jace-xu/Control-esp32/Structure/机械臂_v6/板材/旋转台底板_5mm.SLDPRT

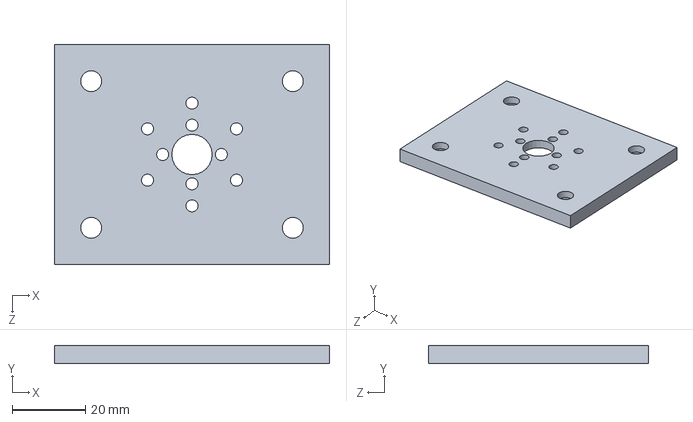
[picture p15: CAD file, 2026-09-05]
Structure/机械臂_v6/板材/旋转台底板_5mm.SLDPRT
75.0 x 5.00 x 60.0 mm
