jace-xu/Control-esp32/Structure/机械臂_v6/购买标准件/丝杆_8_250.SLDPRT

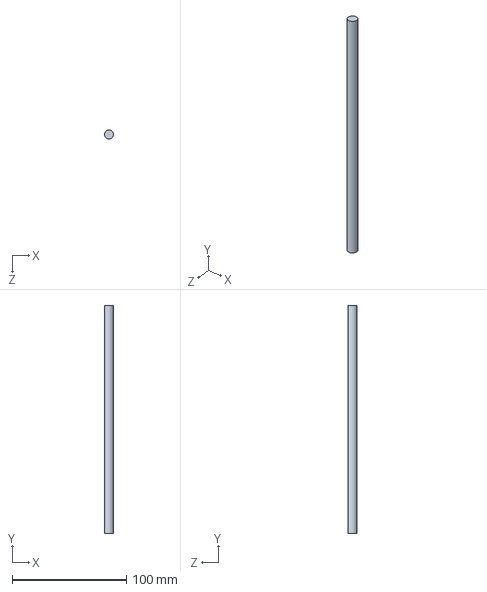
[picture p16: CAD file, 2026-09-05]
Structure/机械臂_v6/购买标准件/丝杆_8_250.SLDPRT
8.00 x 200.0 x 8.00 mm
