jace-xu/Control-esp32/Structure/物料.SLDPRT

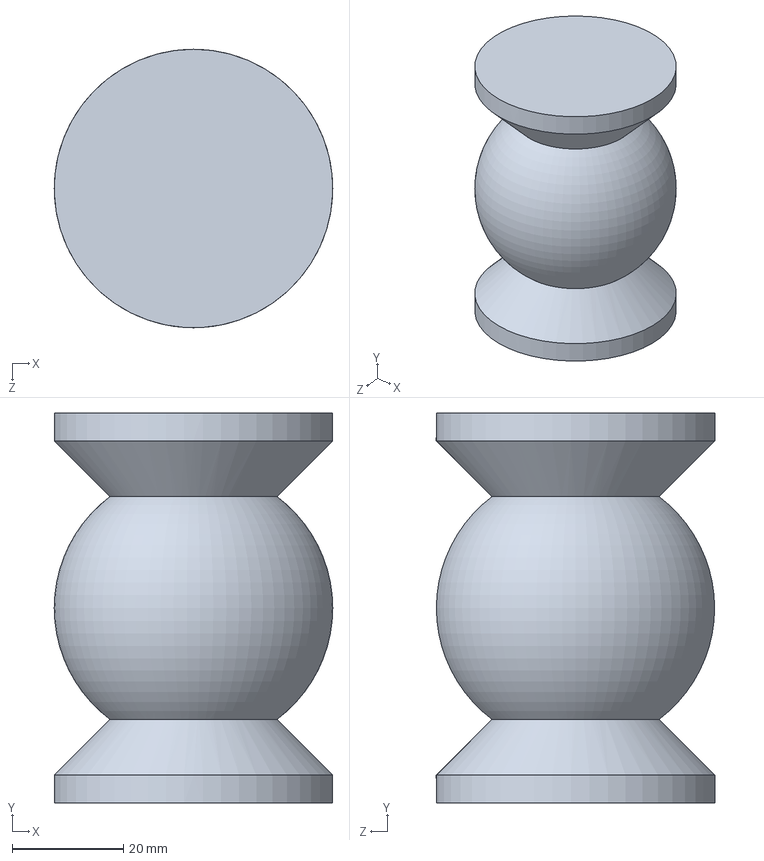
[picture p17: CAD file, 2026-09-05]
Structure/物料.SLDPRT
50.0 x 70.0 x 50.0 mm
