jace-xu/Control-esp32/Structure/物流小车底盘_v6/底盘/板材/电机连接板_后.SLDPRT

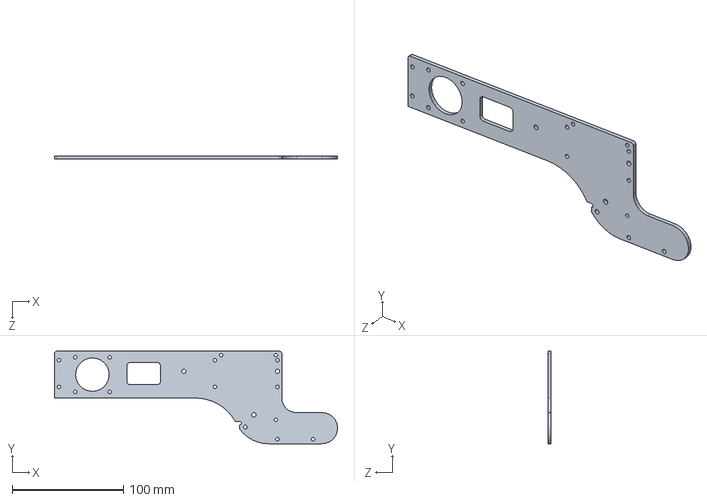
[picture p19: CAD file, 2026-09-05]
Structure/物流小车底盘_v6/底盘/板材/电机连接板_后.SLDPRT
253.9 x 83.0 x 3.00 mm
