jace-xu/Control-esp32/Structure/物流小车底盘_v6/底盘/购买件/麦轮联轴器.SLDPRT

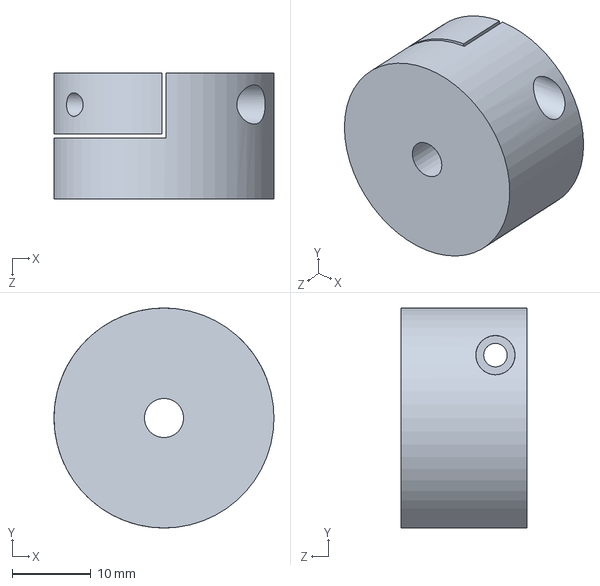
[picture p20: CAD file, 2026-09-05]
Structure/物流小车底盘_v6/底盘/购买件/麦轮联轴器.SLDPRT
28.0 x 28.0 x 16.0 mm
