jace-xu/Control-esp32/Structure/物流小车底盘_v6/标准件/mg996r.SLDPRT

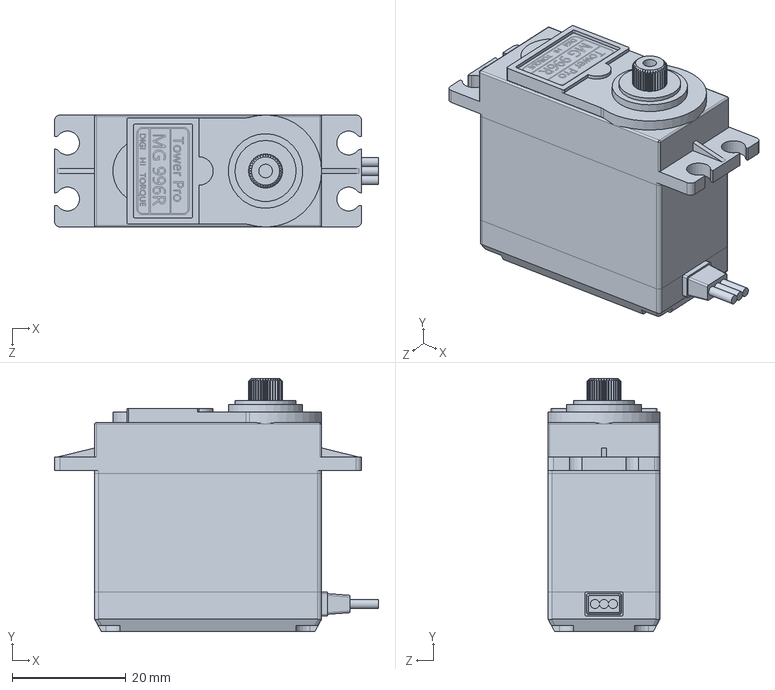
[picture p21: CAD file, 2026-09-05]
Structure/物流小车底盘_v6/标准件/mg996r.SLDPRT
57.0 x 44.5 x 19.7 mm
