jace-xu/Control-esp32/Structure/物流小车底盘_v6/铜柱_m2.5_10.SLDPRT

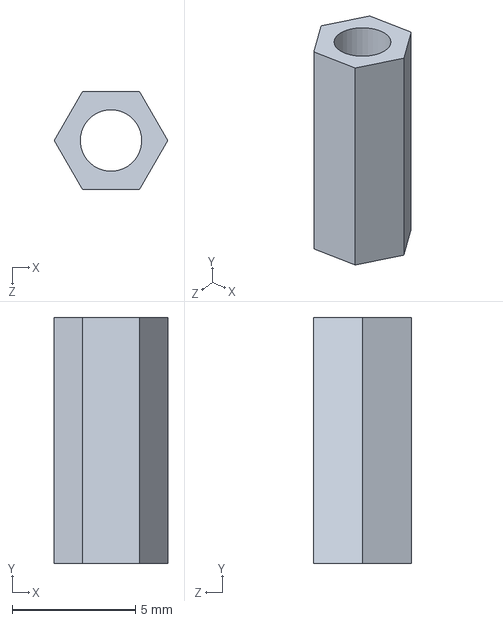
[picture p22: CAD file, 2026-09-05]
Structure/物流小车底盘_v6/铜柱_m2.5_10.SLDPRT
4.62 x 10.0 x 4.00 mm
