jace-xu/Control-esp32/Structure/机械臂_v6/打印件/轴承垫块.SLDPRT

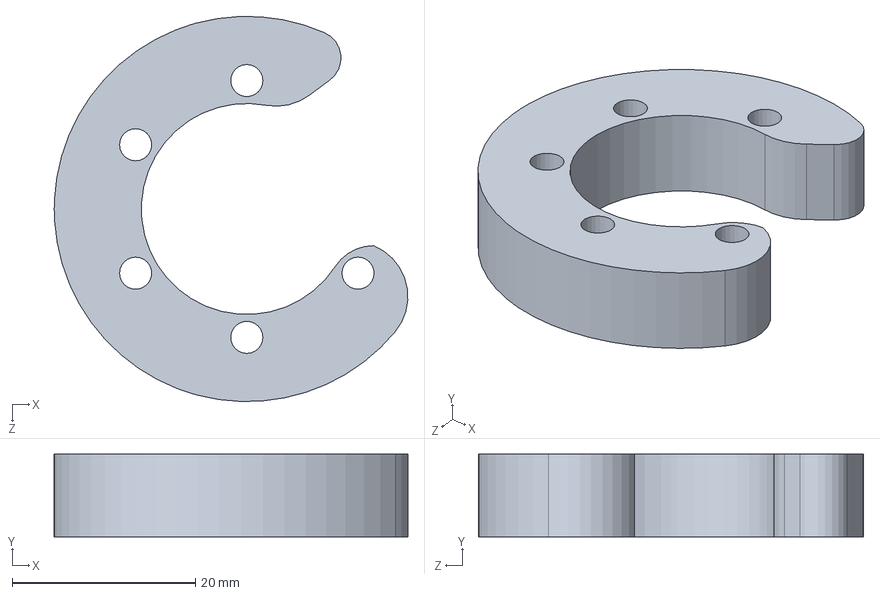
[picture p23: CAD file, 2026-09-05]
Structure/机械臂_v6/打印件/轴承垫块.SLDPRT
38.5 x 9.00 x 42.0 mm
