jace-xu/Control-esp32/Structure/机械臂_v6/板材/夹爪连接板_3mm.SLDPRT

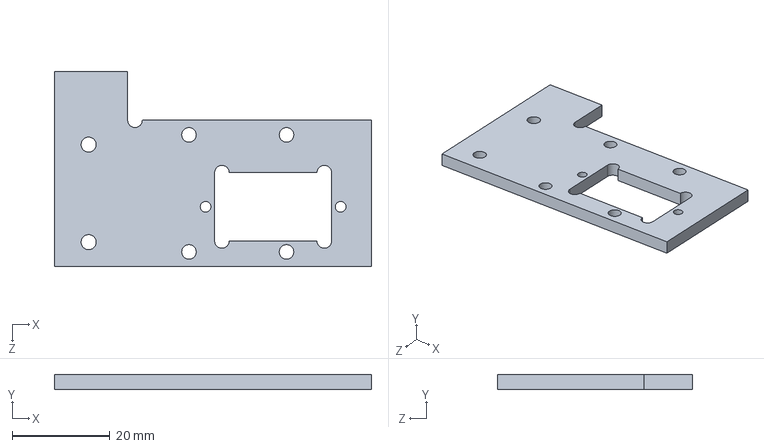
[picture p24: CAD file, 2026-09-05]
Structure/机械臂_v6/板材/夹爪连接板_3mm.SLDPRT
65.0 x 3.00 x 40.0 mm
