jace-xu/Control-esp32/Structure/机械臂_v6/购买标准件/滑块MGN7C_标件_01.SLDPRT

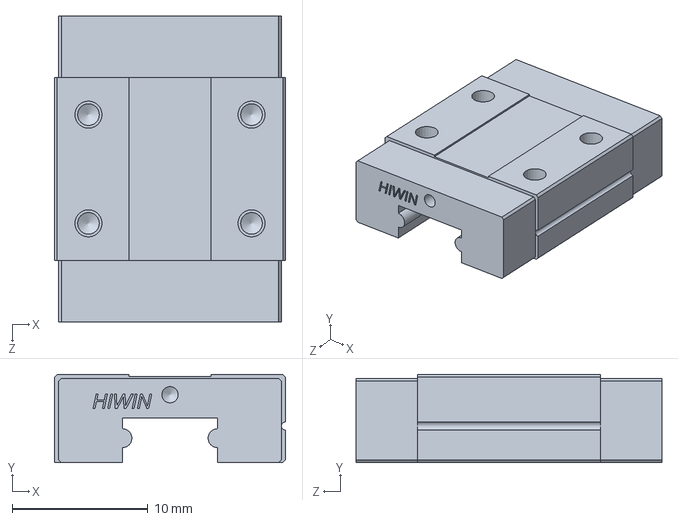
[picture p25: CAD file, 2026-09-05]
Structure/机械臂_v6/购买标准件/滑块MGN7C_标件_01.SLDPRT
17.0 x 6.50 x 22.5 mm
