jace-xu/Control-esp32/Structure/物流小车底盘_v6/底盘/打印件/电机板固定件.SLDPRT

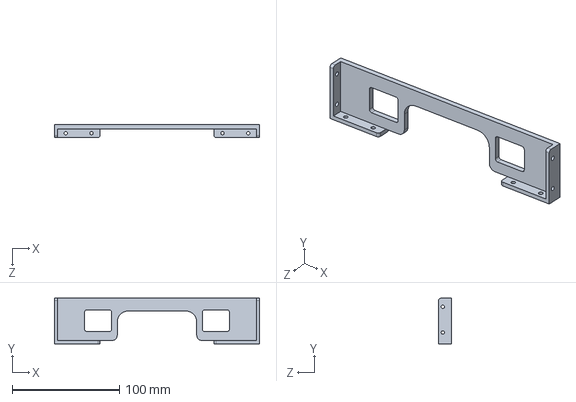
[picture p26: CAD file, 2026-09-05]
Structure/物流小车底盘_v6/底盘/打印件/电机板固定件.SLDPRT
191.0 x 42.5 x 12.0 mm
