jace-xu/Control-esp32/Structure/物流小车底盘_v6/底盘/板材/底板_后.SLDPRT

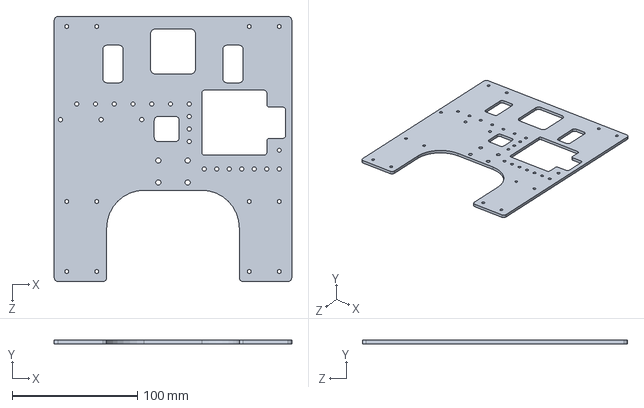
[picture p27: CAD file, 2026-09-05]
Structure/物流小车底盘_v6/底盘/板材/底板_后.SLDPRT
190.0 x 3.00 x 212.0 mm
