jace-xu/Control-esp32/Structure/物流小车底盘_v6/底盘/购买件/60mm麦轮_左.SLDPRT

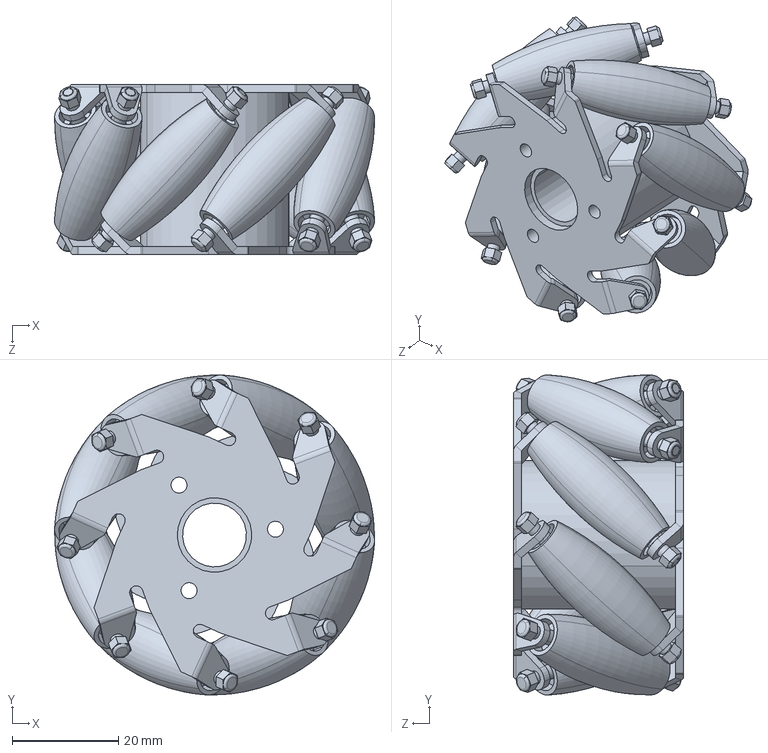
[picture p28: CAD file, 2026-09-05]
Structure/物流小车底盘_v6/底盘/购买件/60mm麦轮_左.SLDPRT
60.1 x 60.1 x 32.0 mm
