jace-xu/Control-esp32/Structure/物流小车底盘_v6/标准件/圆柱齿轮18×1.SLDPRT

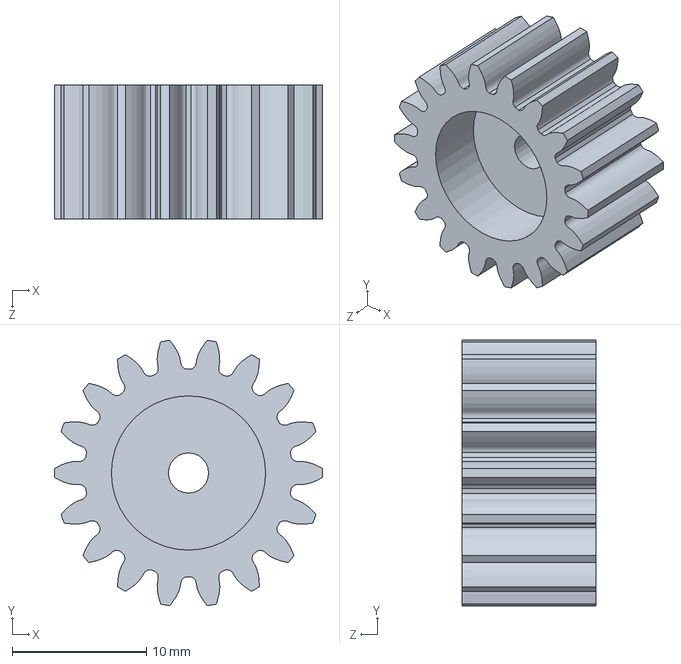
[picture p29: CAD file, 2026-09-05]
Structure/物流小车底盘_v6/标准件/圆柱齿轮18×1.SLDPRT
20.0 x 19.8 x 10.0 mm
