jace-xu/Control-esp32/Structure/物流小车底盘_v6/降压板.SLDPRT

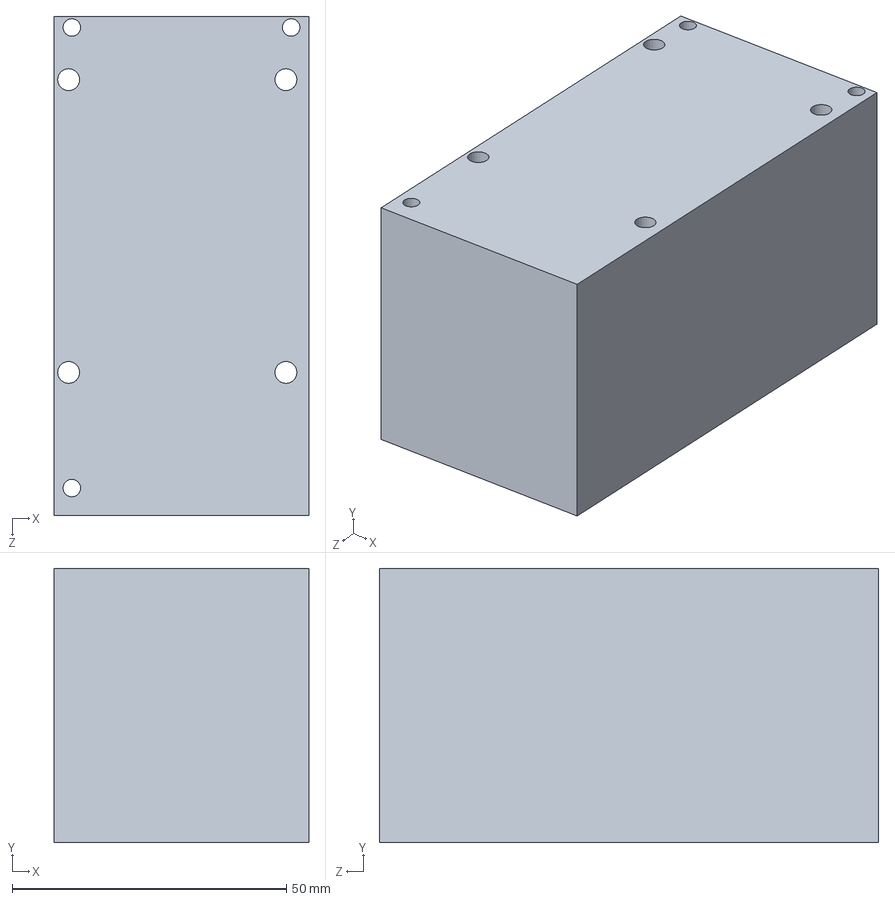
[picture p30: CAD file, 2026-09-05]
Structure/物流小车底盘_v6/降压板.SLDPRT
46.5 x 50.0 x 91.0 mm
