jace-xu/Control-esp32/Structure/机械臂_v6/打印件/z轴机械臂垫块.SLDPRT

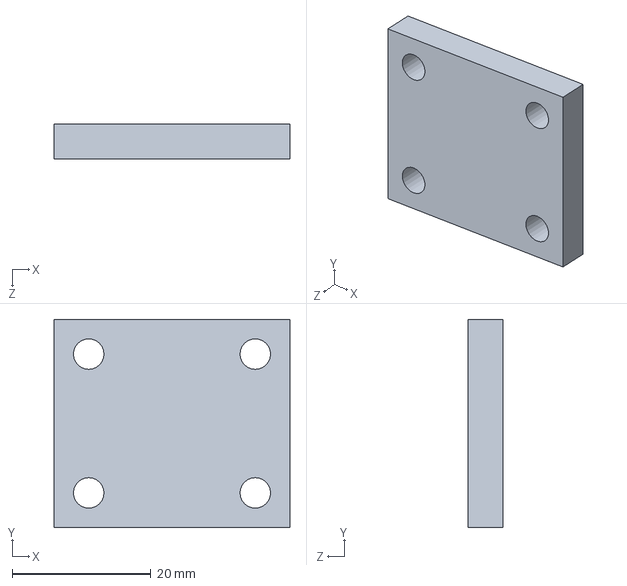
[picture p31: CAD file, 2026-09-05]
Structure/机械臂_v6/打印件/z轴机械臂垫块.SLDPRT
34.0 x 30.0 x 5.00 mm
