jace-xu/Control-esp32/Structure/机械臂_v6/板材/吊臂从动轮外侧固定板_3mm.SLDPRT

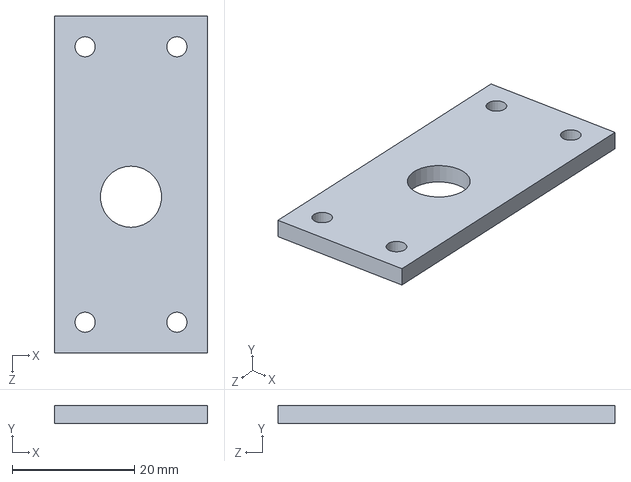
[picture p32: CAD file, 2026-09-05]
Structure/机械臂_v6/板材/吊臂从动轮外侧固定板_3mm.SLDPRT
25.0 x 3.00 x 55.0 mm
