jace-xu/Control-esp32/Structure/机械臂_v6/购买标准件/mg90舵盘.SLDPRT

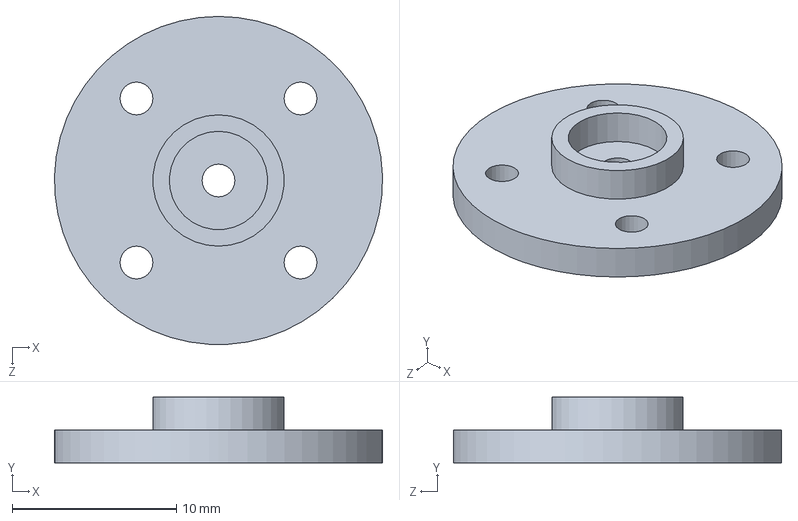
[picture p33: CAD file, 2026-09-05]
Structure/机械臂_v6/购买标准件/mg90舵盘.SLDPRT
20.0 x 4.00 x 20.0 mm
