jace-xu/Control-esp32/Structure/物流小车底盘_v6/Mirror铁块托盘.SLDPRT

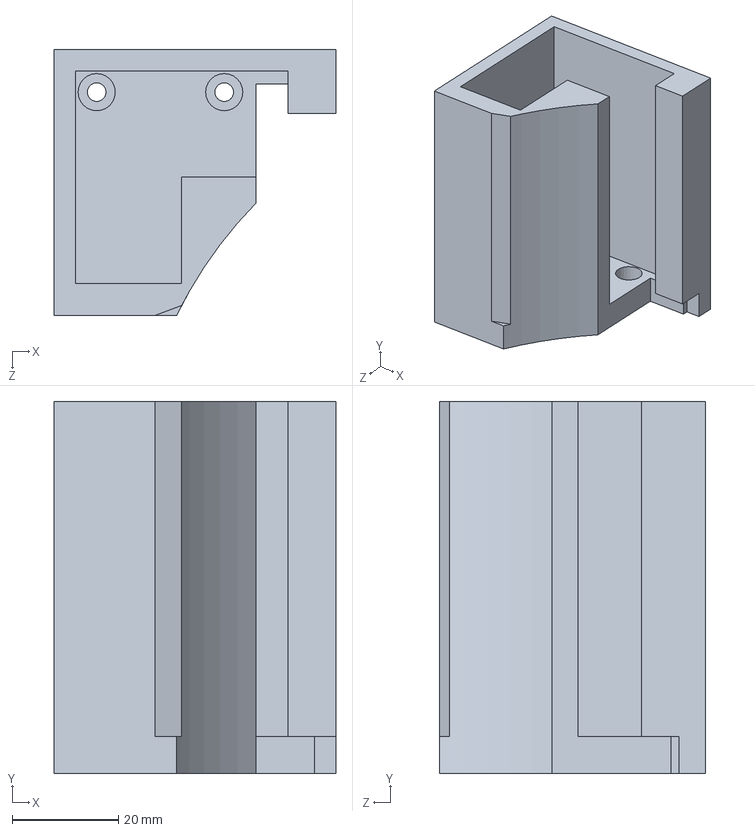
[picture p34: CAD file, 2026-09-05]
Structure/物流小车底盘_v6/Mirror铁块托盘.SLDPRT
53.0 x 70.0 x 50.0 mm
