jace-xu/Control-esp32/Structure/物流小车底盘_v6/底盘/打印件/层连接件.SLDPRT

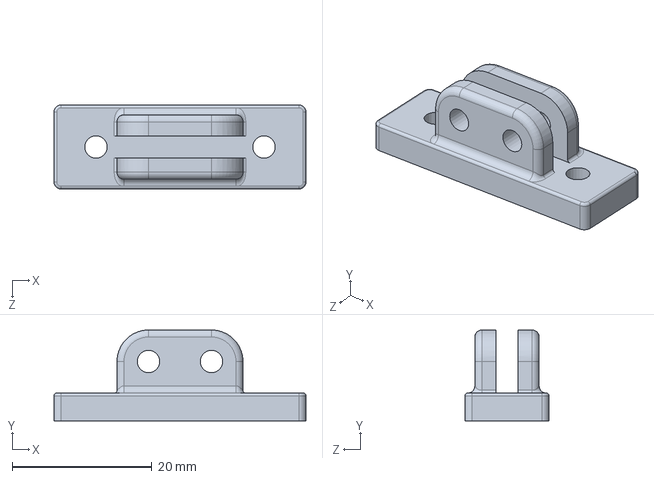
[picture p35: CAD file, 2026-09-05]
Structure/物流小车底盘_v6/底盘/打印件/层连接件.SLDPRT
36.0 x 13.0 x 12.0 mm
