jace-xu/Control-esp32/Structure/物流小车底盘_v6/底盘/标准件/六角防松锁紧螺母.SLDPRT

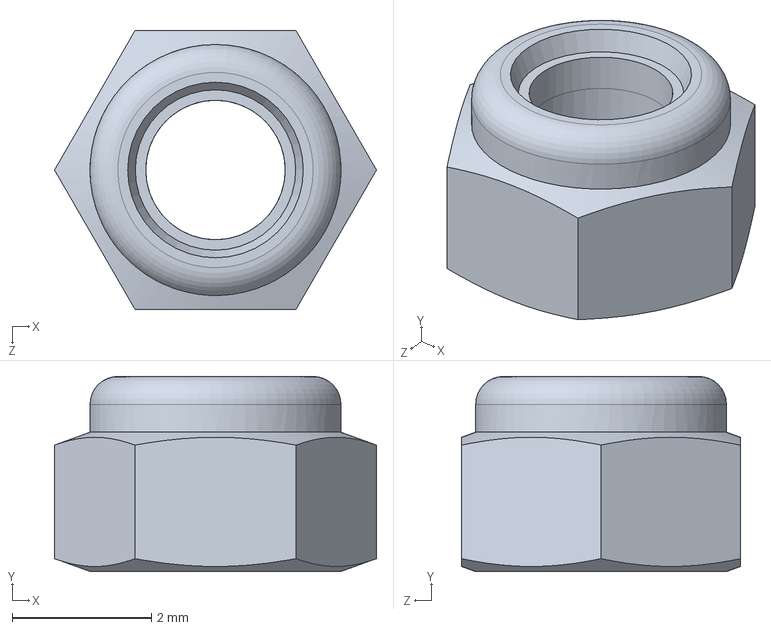
[picture p37: CAD file, 2026-09-05]
Structure/物流小车底盘_v6/底盘/标准件/六角防松锁紧螺母.SLDPRT
4.62 x 2.80 x 4.00 mm
