jace-xu/Control-esp32/Structure/物流小车底盘_v6/底盘/购买件/思岚c1.SLDPRT

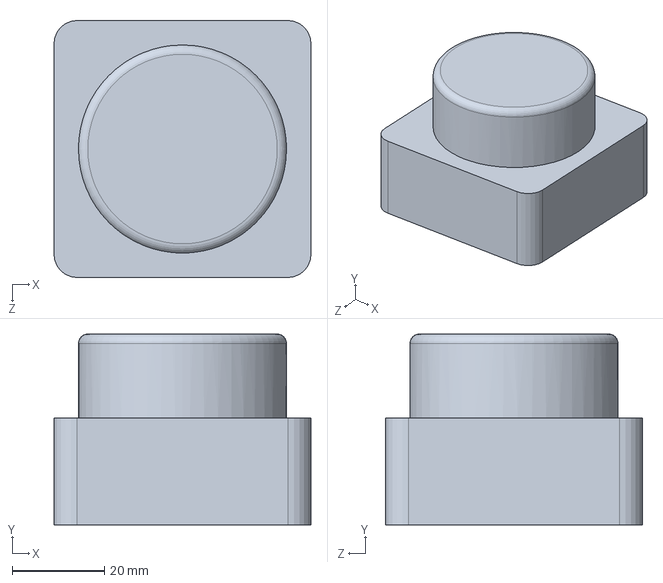
[picture p38: CAD file, 2026-09-05]
Structure/物流小车底盘_v6/底盘/购买件/思岚c1.SLDPRT
55.6 x 41.3 x 55.6 mm
