jace-xu/Control-esp32/Structure/物流小车底盘_v6/标准件/六角防松锁紧螺母M4.SLDPRT

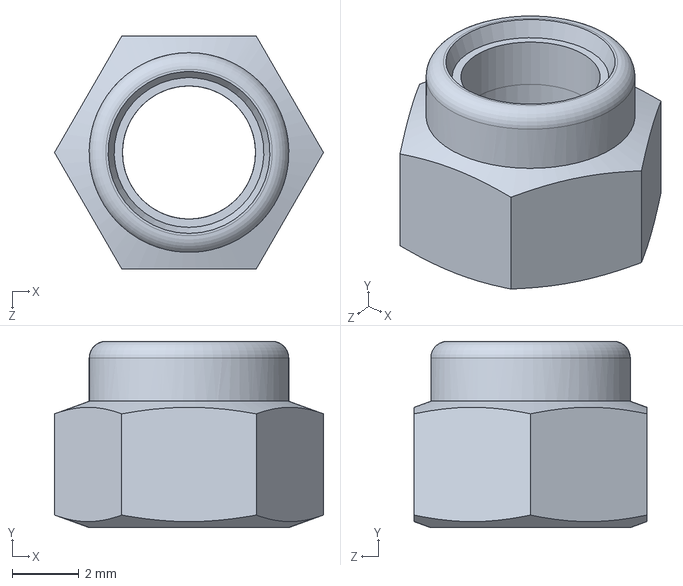
[picture p39: CAD file, 2026-09-05]
Structure/物流小车底盘_v6/标准件/六角防松锁紧螺母M4.SLDPRT
8.08 x 5.60 x 7.00 mm
