jace-xu/Control-esp32/Structure/机械臂_v6/打印件/夹爪右.SLDPRT

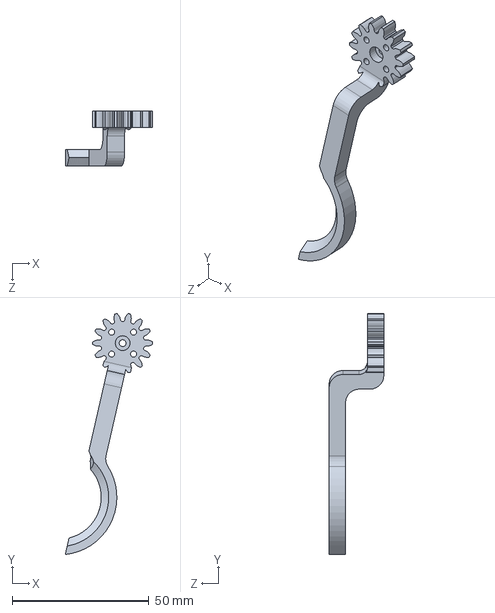
[picture p40: CAD file, 2026-09-05]
Structure/机械臂_v6/打印件/夹爪右.SLDPRT
31.9 x 88.0 x 20.0 mm
