jace-xu/Control-esp32/Structure/机械臂_v6/板材/底座旋转电机板_5mm.SLDPRT

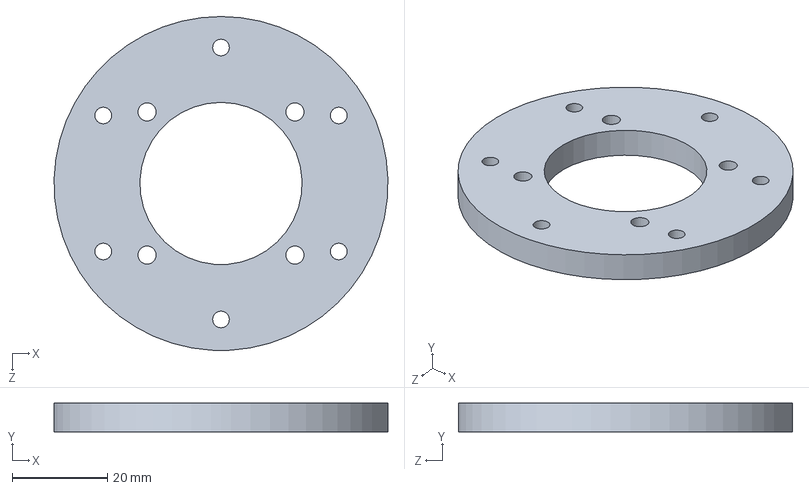
[picture p41: CAD file, 2026-09-05]
Structure/机械臂_v6/板材/底座旋转电机板_5mm.SLDPRT
70.0 x 6.00 x 70.0 mm
