jace-xu/Control-esp32/Structure/机械臂_v6/购买标准件/同步带_10mm.SLDPRT

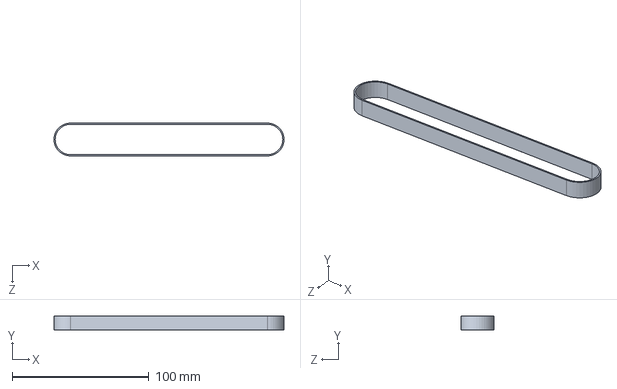
[picture p42: CAD file, 2026-09-05]
Structure/机械臂_v6/购买标准件/同步带_10mm.SLDPRT
168.4 x 10.0 x 24.0 mm
