jace-xu/Control-esp32/Structure/物流小车底盘_v6/底盘/板材/层连接板_1.SLDPRT

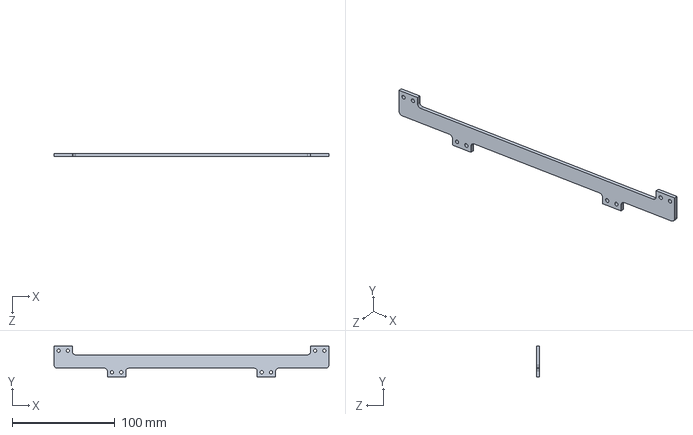
[picture p43: CAD file, 2026-09-05]
Structure/物流小车底盘_v6/底盘/板材/层连接板_1.SLDPRT
268.0 x 30.0 x 3.00 mm
