jace-xu/Control-esp32/Structure/物流小车底盘_v6/底盘/购买件/42步进电机.SLDPRT

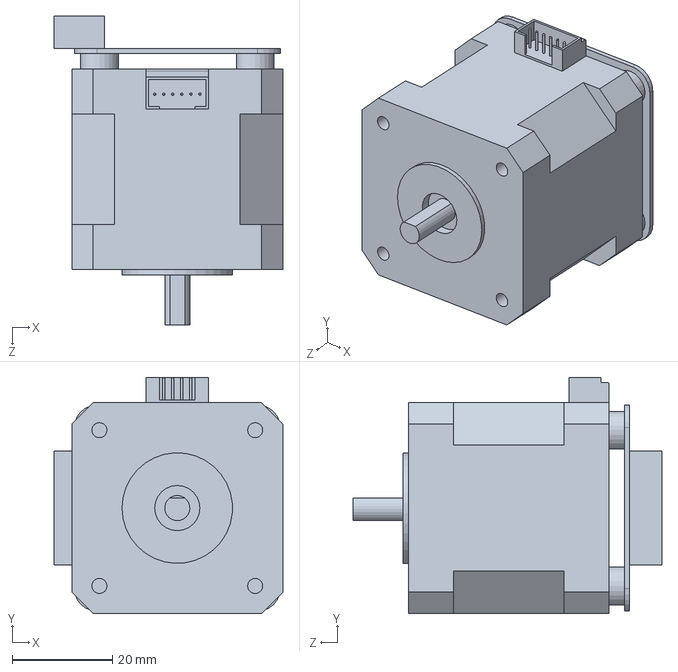
[picture p44: CAD file, 2026-09-05]
Structure/物流小车底盘_v6/底盘/购买件/42步进电机.SLDPRT
45.5 x 47.0 x 61.5 mm
