jace-xu/Control-esp32/Structure/机械臂_v6/打印件/舵机支架.SLDPRT

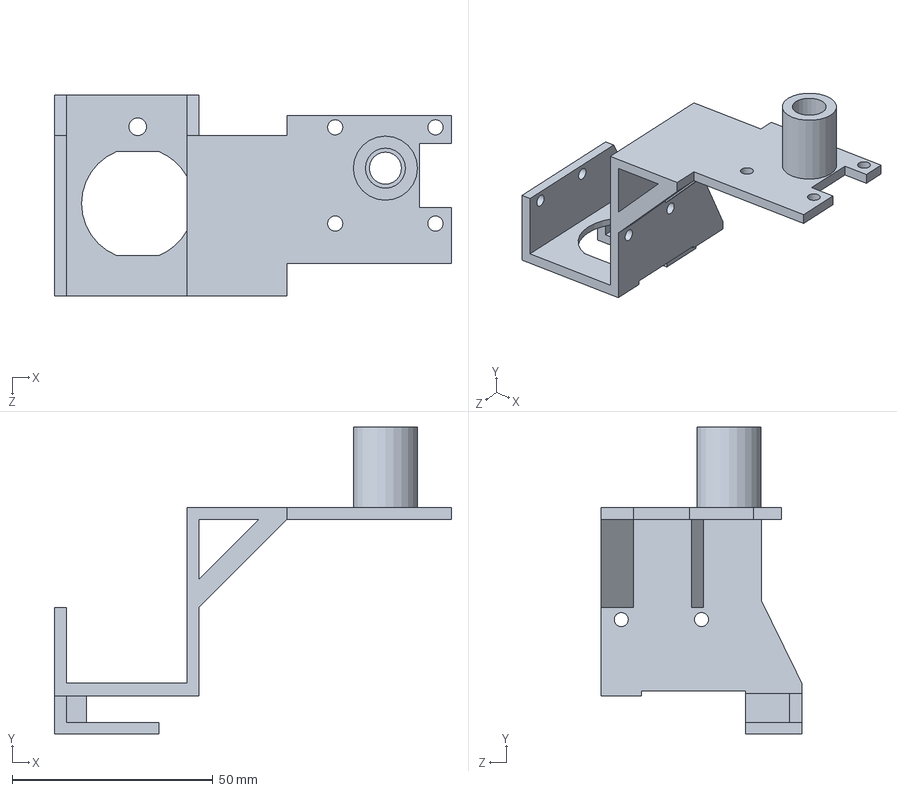
[picture p45: CAD file, 2026-09-05]
Structure/机械臂_v6/打印件/舵机支架.SLDPRT
99.0 x 76.5 x 50.0 mm
