jace-xu/Control-esp32/Structure/机械臂_v6/板材/底座板_3mm.SLDPRT

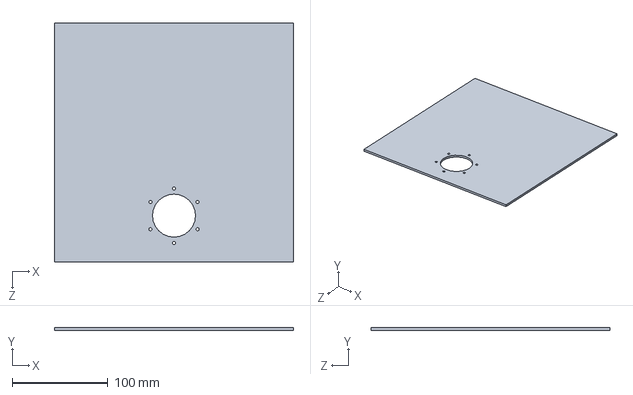
[picture p46: CAD file, 2026-09-05]
Structure/机械臂_v6/板材/底座板_3mm.SLDPRT
250.0 x 3.00 x 250.0 mm
