jace-xu/Control-esp32/Structure/机械臂_v6/购买标准件/同步带轮_24H3M.SLDPRT

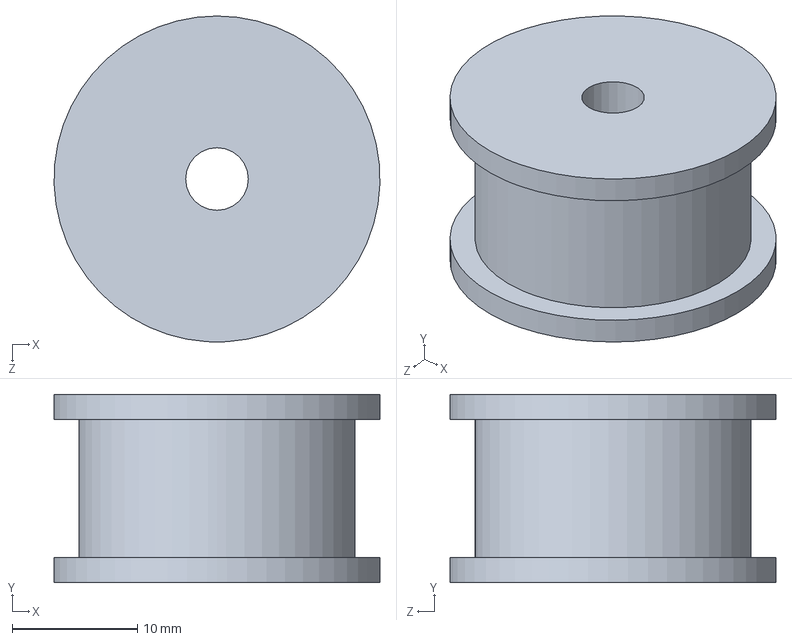
[picture p47: CAD file, 2026-09-05]
Structure/机械臂_v6/购买标准件/同步带轮_24H3M.SLDPRT
26.0 x 15.0 x 26.0 mm
