jace-xu/Control-esp32/Structure/物流小车底盘_v6/底盘/购买件/悬挂_半.SLDPRT

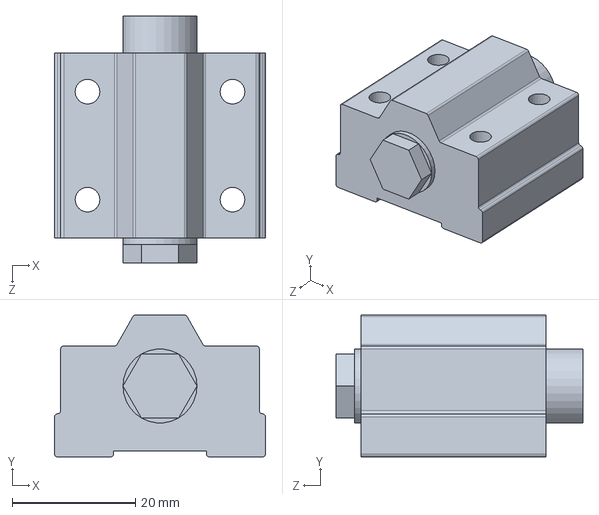
[picture p48: CAD file, 2026-09-05]
Structure/物流小车底盘_v6/底盘/购买件/悬挂_半.SLDPRT
34.2 x 23.0 x 40.0 mm
