jace-xu/Control-esp32/Structure/物流小车底盘_v6/标准件/内六角圆柱头螺钉M4-10.SLDPRT

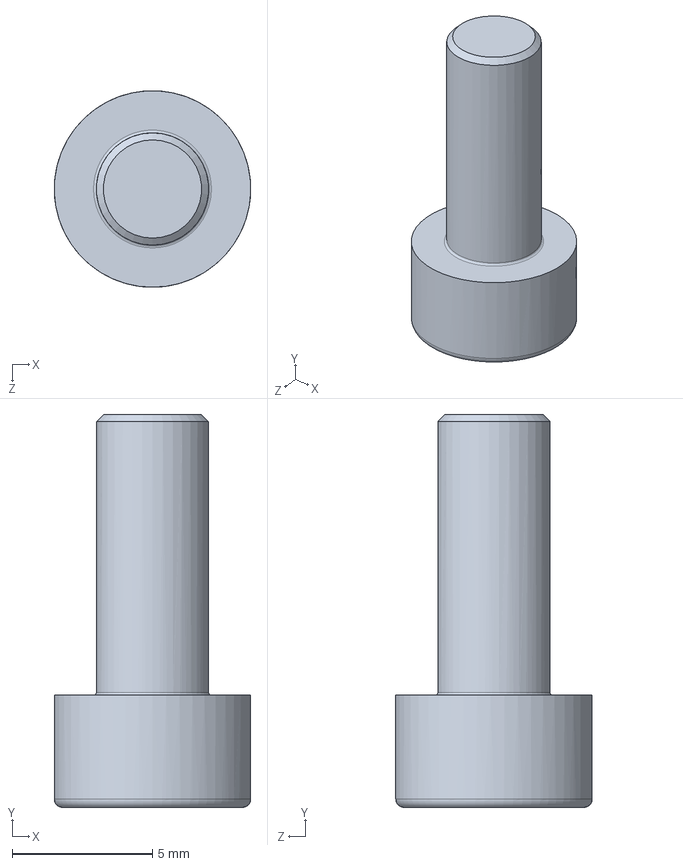
[picture p49: CAD file, 2026-09-05]
Structure/物流小车底盘_v6/标准件/内六角圆柱头螺钉M4-10.SLDPRT
7.00 x 14.0 x 7.00 mm
