jace-xu/Control-esp32/Structure/物流小车底盘_v6/电池仓.SLDPRT

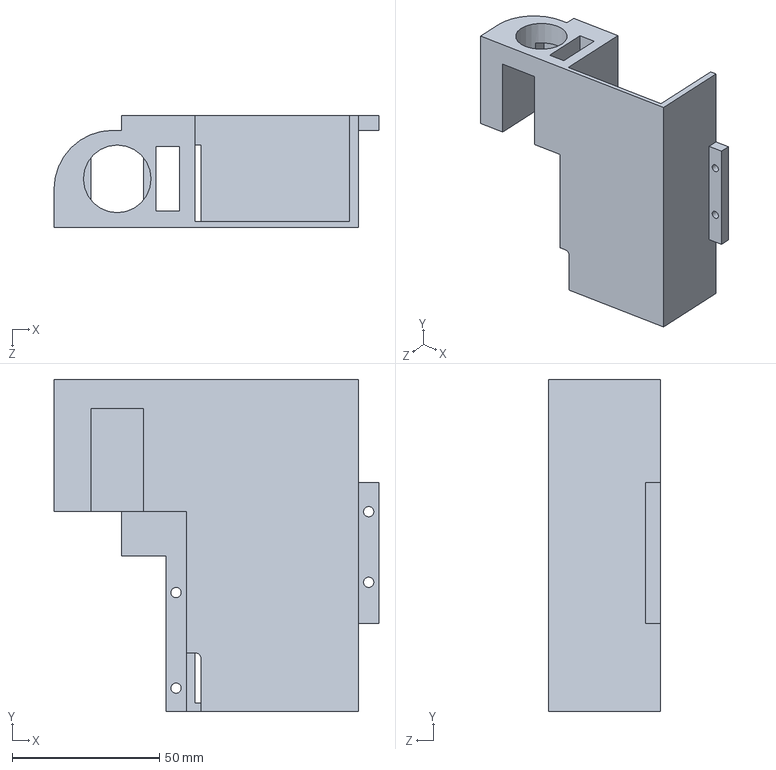
[picture p50: CAD file, 2026-09-05]
Structure/物流小车底盘_v6/电池仓.SLDPRT
110.5 x 113.0 x 38.0 mm
