jace-xu/Control-esp32/Structure/机械臂_v6/打印件/底部电机垫块.SLDPRT

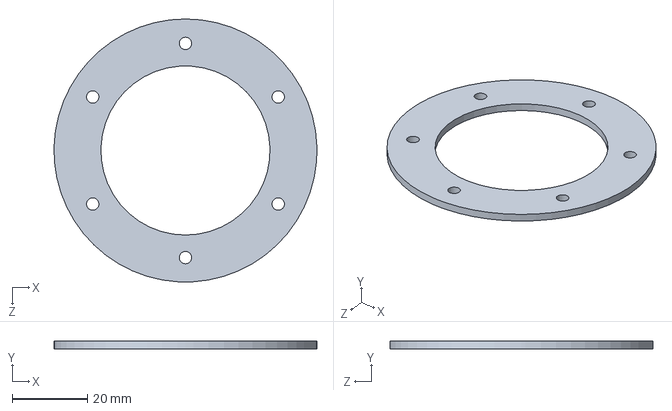
[picture p51: CAD file, 2026-09-05]
Structure/机械臂_v6/打印件/底部电机垫块.SLDPRT
70.0 x 2.00 x 70.0 mm
