jace-xu/Control-esp32/Structure/机械臂_v6/板材/夹爪固定板_3mm.SLDPRT

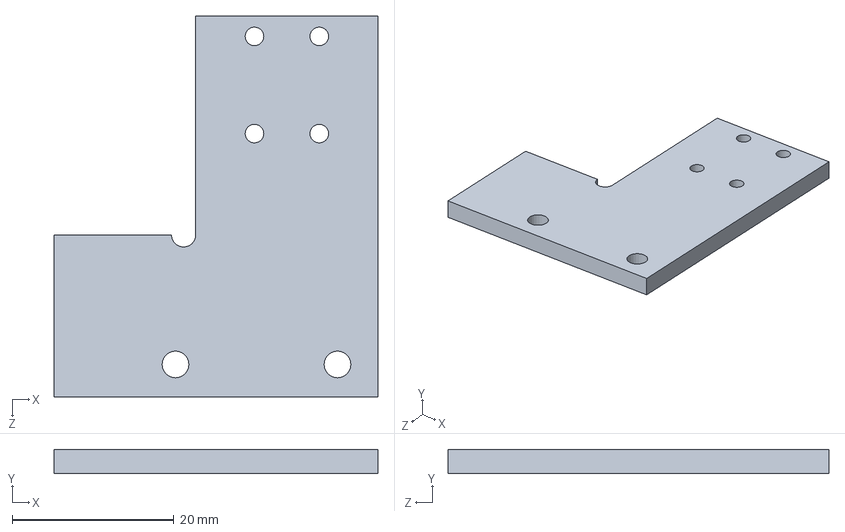
[picture p52: CAD file, 2026-09-05]
Structure/机械臂_v6/板材/夹爪固定板_3mm.SLDPRT
40.0 x 3.00 x 47.0 mm
