jace-xu/Control-esp32/Structure/机械臂_v6/购买标准件/丝杆螺母.SLDPRT

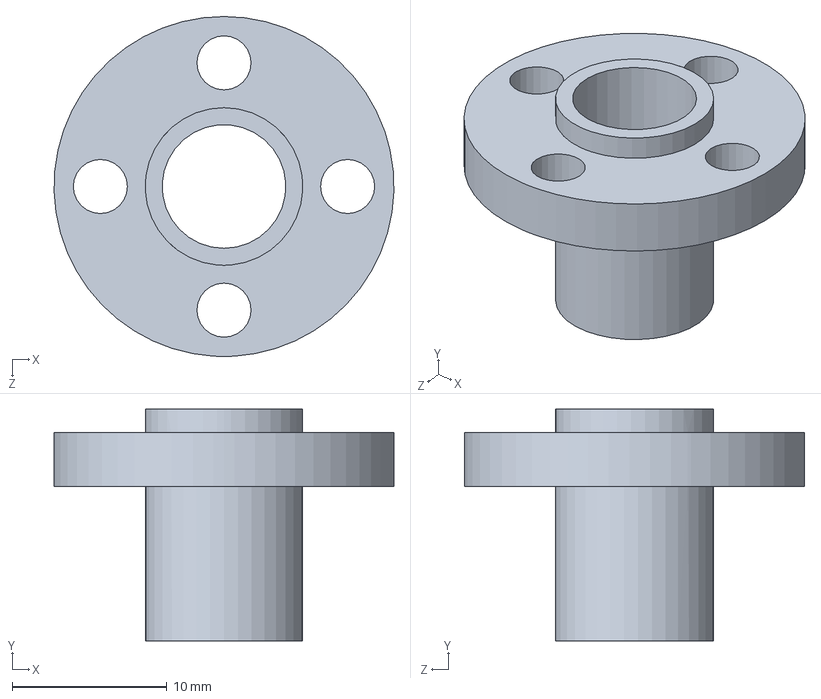
[picture p53: CAD file, 2026-09-05]
Structure/机械臂_v6/购买标准件/丝杆螺母.SLDPRT
22.0 x 15.0 x 22.0 mm
