jace-xu/Control-esp32/Structure/物流小车底盘_v6/底盘/购买件/牛眼轮.SLDPRT

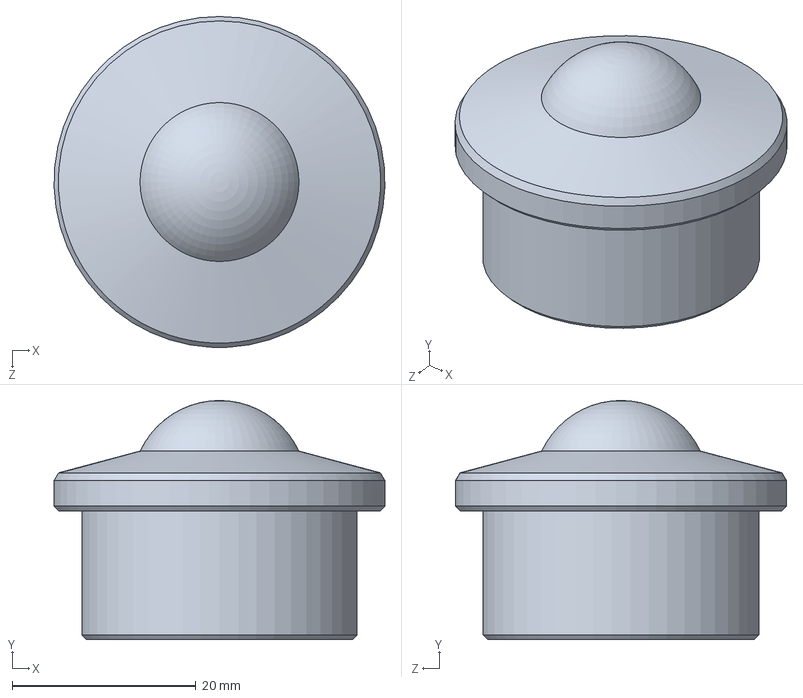
[picture p54: CAD file, 2026-09-05]
Structure/物流小车底盘_v6/底盘/购买件/牛眼轮.SLDPRT
36.0 x 26.0 x 36.0 mm
