jace-xu/Control-esp32/Structure/物流小车底盘_v6/标准件/内六角圆柱头螺钉M3-7.SLDPRT

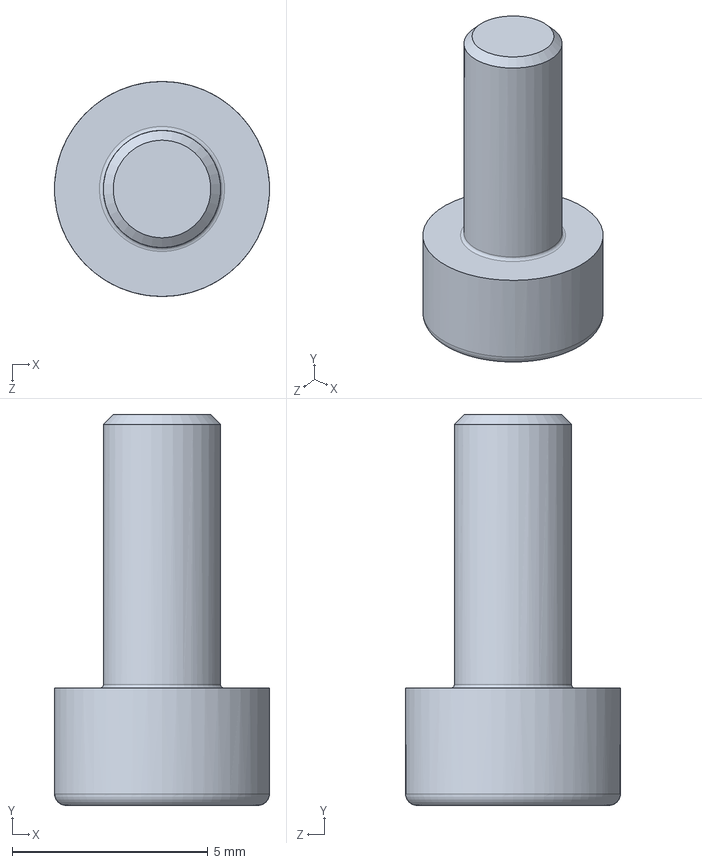
[picture p55: CAD file, 2026-09-05]
Structure/物流小车底盘_v6/标准件/内六角圆柱头螺钉M3-7.SLDPRT
5.50 x 10.0 x 5.50 mm
