jace-xu/Control-esp32/Structure/机械臂_v6/打印件/下部轴承底板.SLDPRT

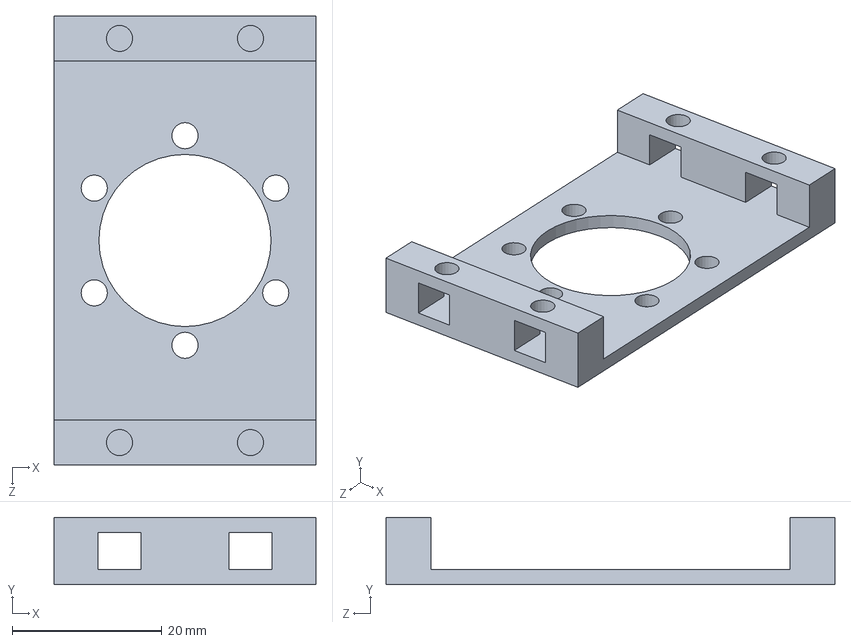
[picture p56: CAD file, 2026-09-05]
Structure/机械臂_v6/打印件/下部轴承底板.SLDPRT
35.0 x 9.00 x 60.0 mm
