jace-xu/Control-esp32/Structure/机械臂_v6/板材/型材顶部板_3mm.SLDPRT

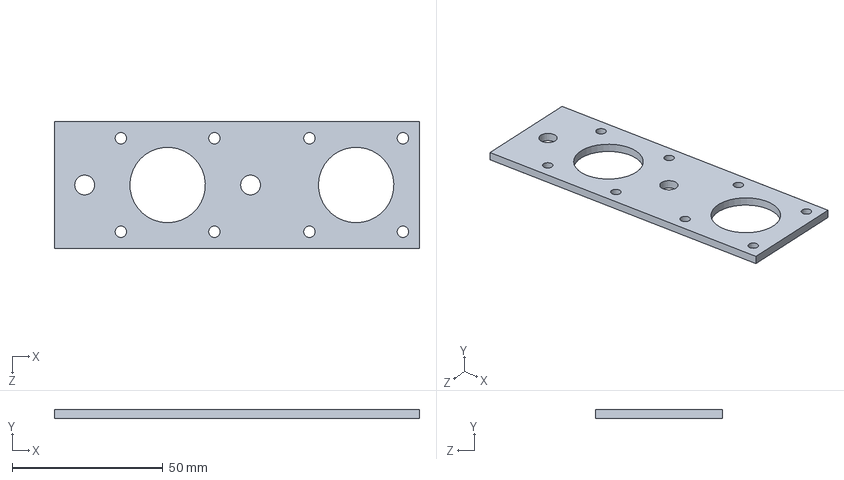
[picture p57: CAD file, 2026-09-05]
Structure/机械臂_v6/板材/型材顶部板_3mm.SLDPRT
121.0 x 3.00 x 42.0 mm
