jace-xu/Control-esp32/Structure/机械臂_v6/购买标准件/ZDT_X42_L40Motor.SLDPRT

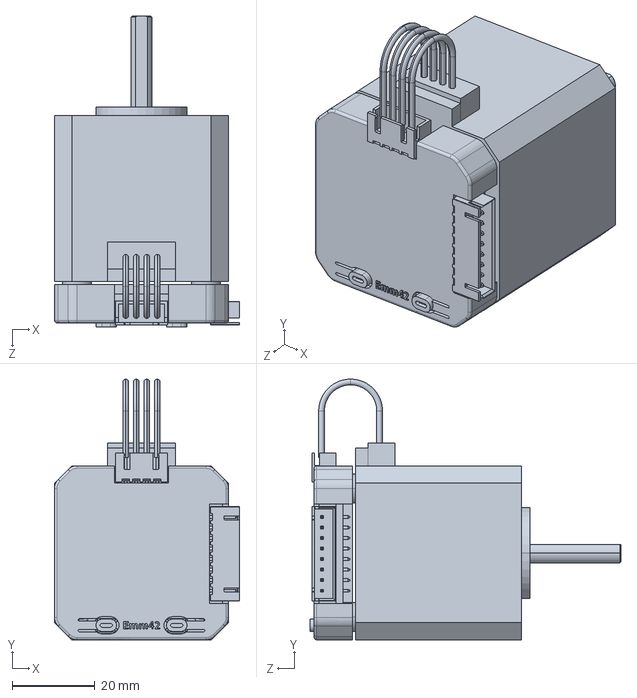
[picture p58: CAD file, 2026-09-05]
Structure/机械臂_v6/购买标准件/ZDT_X42_L40Motor.SLDPRT
44.7 x 62.9 x 75.0 mm
