jace-xu/Control-esp32/Structure/物流小车底盘_v6/Mirror下层铁块支架.SLDPRT

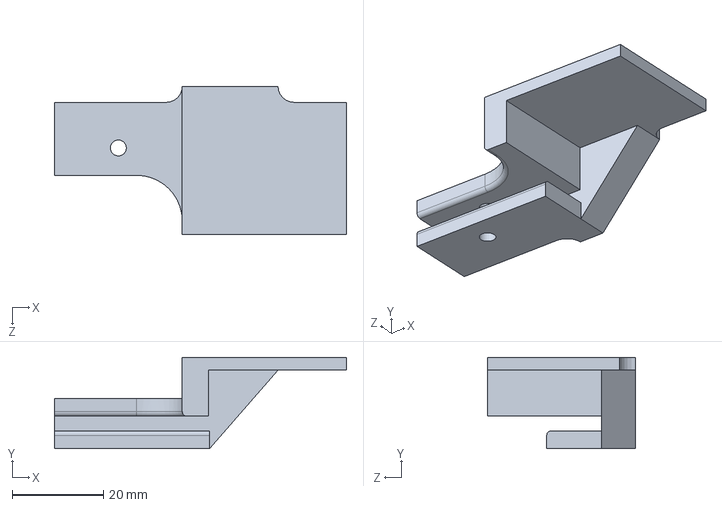
[picture p59: CAD file, 2026-09-05]
Structure/物流小车底盘_v6/Mirror下层铁块支架.SLDPRT
64.0 x 20.0 x 32.5 mm
