jace-xu/Control-esp32/Structure/物流小车底盘_v6/标准件/平垫圈-A级.SLDPRT

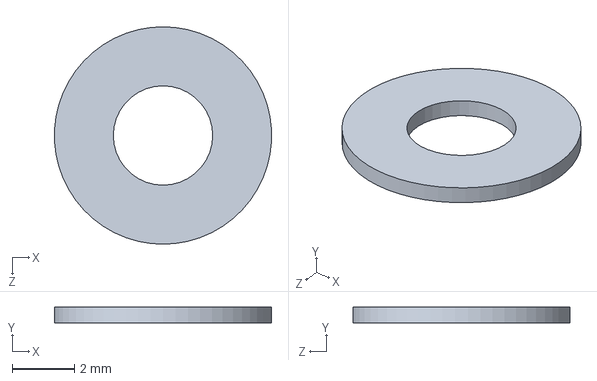
[picture p60: CAD file, 2026-09-05]
Structure/物流小车底盘_v6/标准件/平垫圈-A级.SLDPRT
6.99 x 0.5 x 7.00 mm
