jace-xu/Control-esp32/Structure/机械臂_v6/打印件/夹爪左.SLDPRT

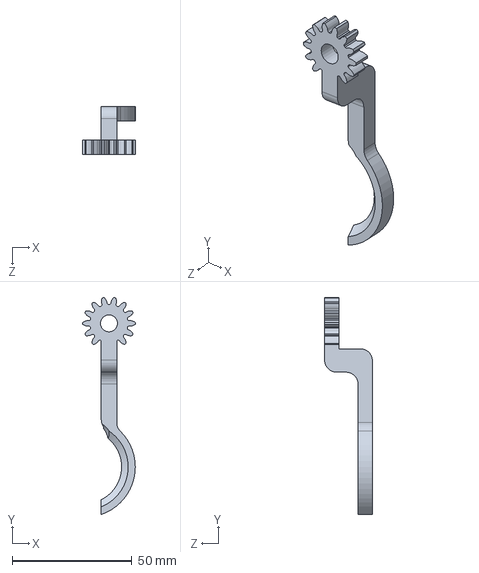
[picture p61: CAD file, 2026-09-05]
Structure/机械臂_v6/打印件/夹爪左.SLDPRT
22.0 x 90.7 x 20.0 mm
