jace-xu/Control-esp32/Structure/机械臂_v6/板材/夹爪背板_3mm_修改前.SLDPRT

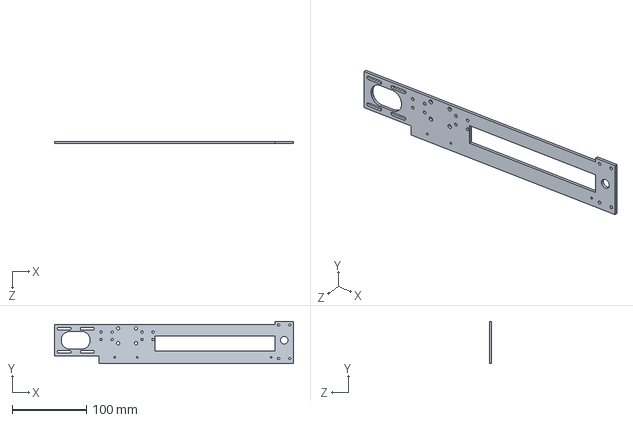
[picture p62: CAD file, 2026-09-05]
Structure/机械臂_v6/板材/夹爪背板_3mm_修改前.SLDPRT
321.0 x 57.0 x 3.00 mm
