jace-xu/Control-esp32/Structure/机械臂_v6/购买标准件/轴承_5.SLDPRT

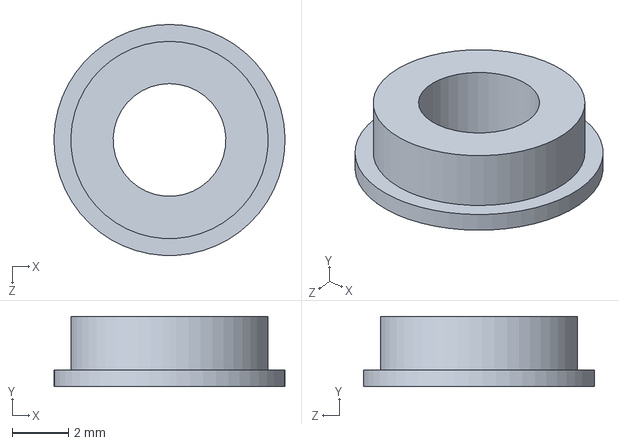
[picture p63: CAD file, 2026-09-05]
Structure/机械臂_v6/购买标准件/轴承_5.SLDPRT
8.20 x 2.50 x 8.20 mm
