jace-xu/Control-esp32/Structure/物流小车底盘_v6/板材.SLDPRT

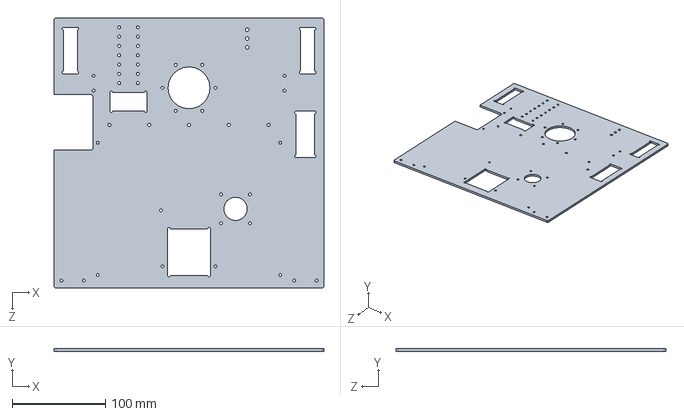
[picture p64: CAD file, 2026-09-05]
Structure/物流小车底盘_v6/板材.SLDPRT
290.0 x 3.00 x 290.0 mm
