jace-xu/Control-esp32/Structure/机械臂_v6/板材/丝杆轴承安装板_3mm.SLDPRT

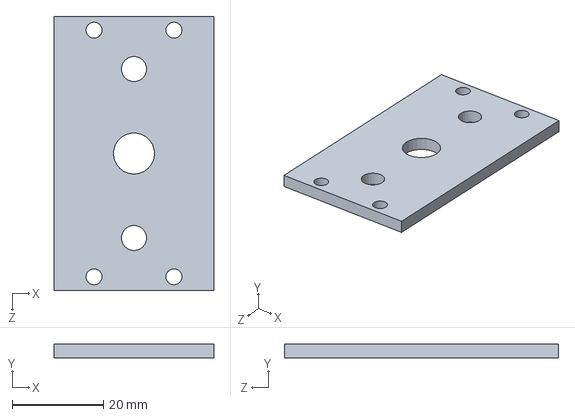
[picture p66: CAD file, 2026-09-05]
Structure/机械臂_v6/板材/丝杆轴承安装板_3mm.SLDPRT
35.0 x 3.00 x 60.0 mm
