jace-xu/Control-esp32/Structure/机械臂_v6/购买标准件/六面螺母_板材连接_6mm.SLDPRT

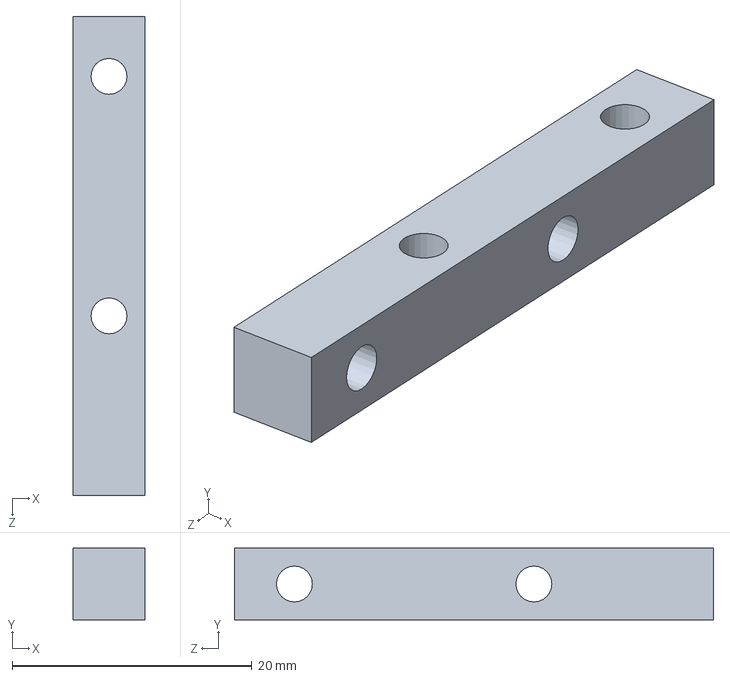
[picture p67: CAD file, 2026-09-05]
Structure/机械臂_v6/购买标准件/六面螺母_板材连接_6mm.SLDPRT
6.00 x 6.00 x 40.0 mm
