jace-xu/Control-esp32/Structure/物流小车底盘_v6/ZDT扩展.SLDPRT

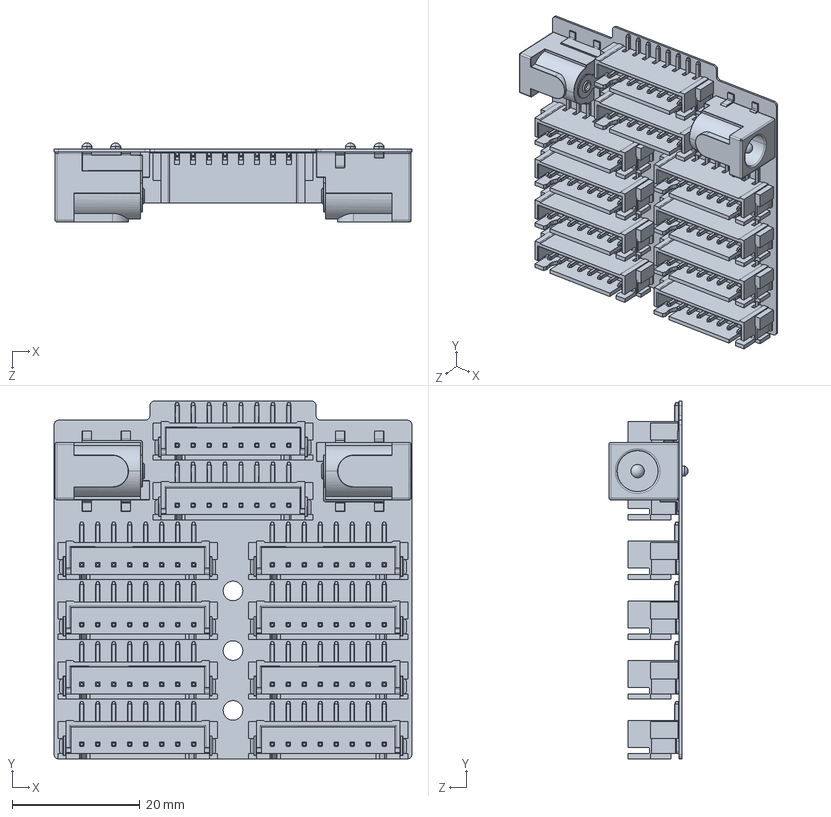
[picture p68: CAD file, 2026-09-05]
Structure/物流小车底盘_v6/ZDT扩展.SLDPRT
56.0 x 56.0 x 12.4 mm
