jace-xu/Control-esp32/Structure/机械臂_v6/板材/夹爪背板_3mm.SLDPRT

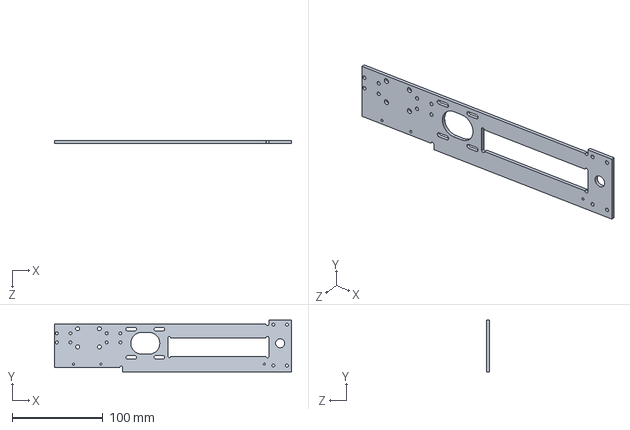
[picture p69: CAD file, 2026-09-05]
Structure/机械臂_v6/板材/夹爪背板_3mm.SLDPRT
261.0 x 57.0 x 3.00 mm
