jace-xu/Control-esp32/Structure/机械臂_v6/购买标准件/法兰轴承_10_5.SLDPRT

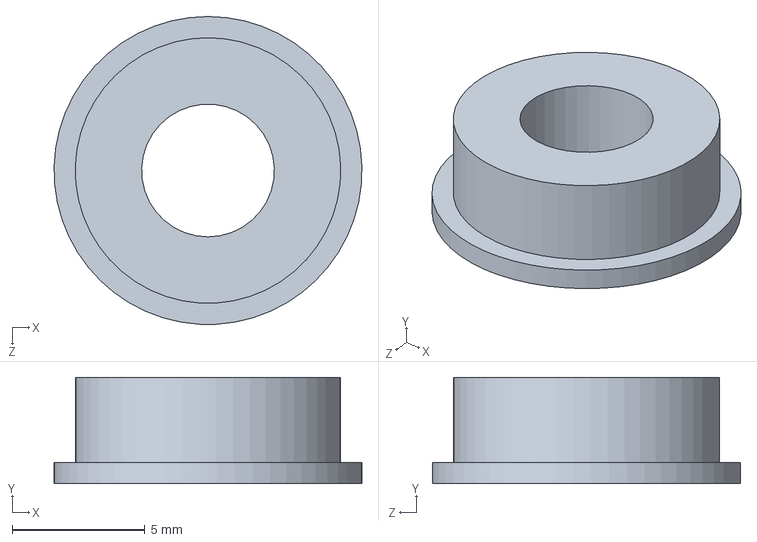
[picture p70: CAD file, 2026-09-05]
Structure/机械臂_v6/购买标准件/法兰轴承_10_5.SLDPRT
11.6 x 4.00 x 11.6 mm
