jace-xu/Control-esp32/Structure/物流小车底盘_v6/标准件/同步带.SLDPRT

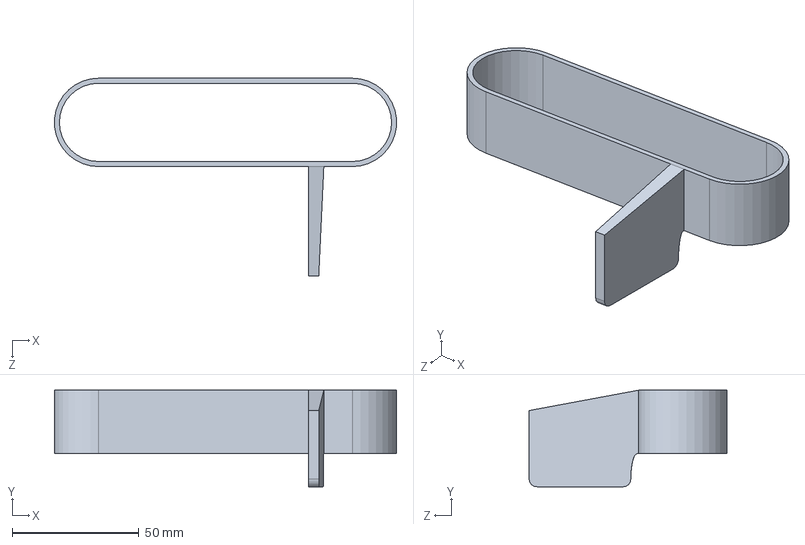
[picture p71: CAD file, 2026-09-05]
Structure/物流小车底盘_v6/标准件/同步带.SLDPRT
134.7 x 38.0 x 77.8 mm
