jace-xu/Control-esp32/Structure/物流小车底盘_v6/齿条连接件_顶板.SLDPRT

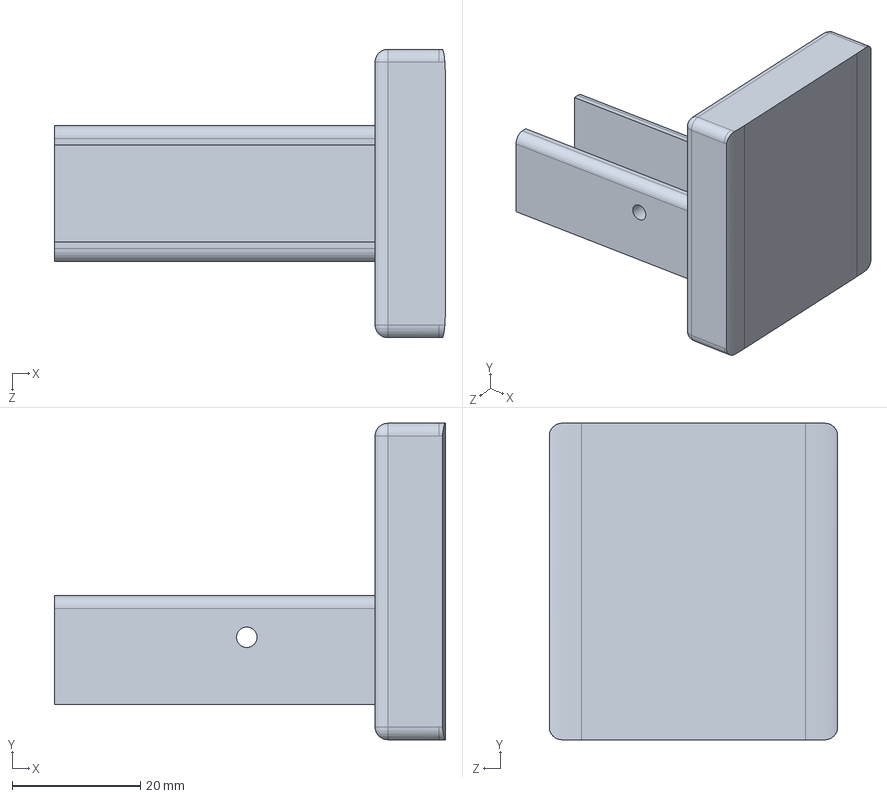
[picture p72: CAD file, 2026-09-05]
Structure/物流小车底盘_v6/齿条连接件_顶板.SLDPRT
61.0 x 49.4 x 45.0 mm
