jace-xu/Control-esp32/Structure/机械臂_v6/购买标准件/联轴器_顶部.SLDPRT

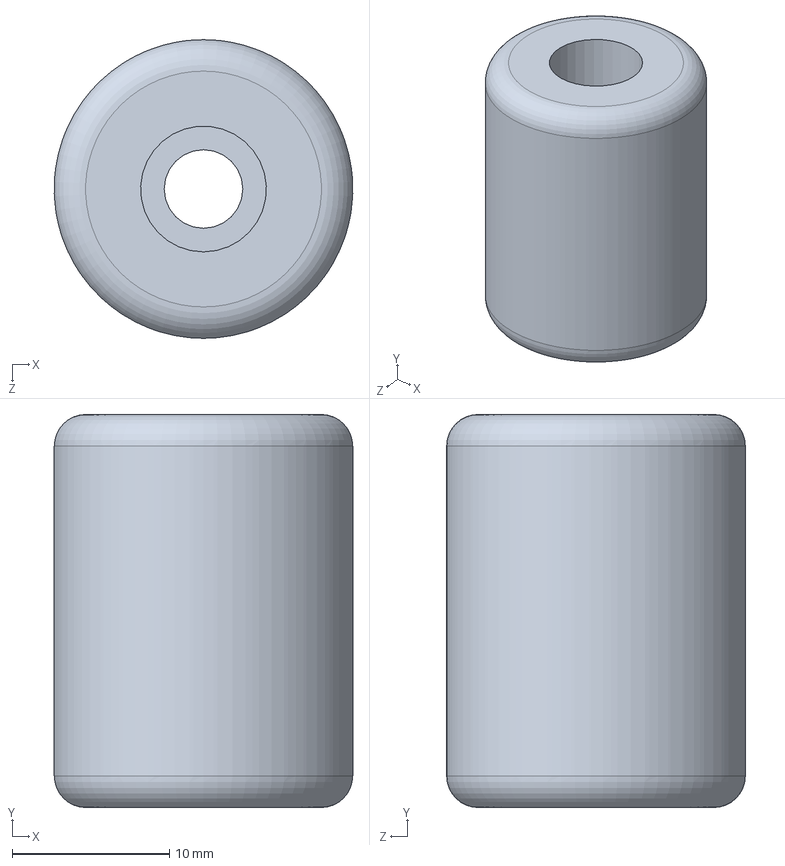
[picture p73: CAD file, 2026-09-05]
Structure/机械臂_v6/购买标准件/联轴器_顶部.SLDPRT
19.0 x 25.0 x 19.0 mm
