jace-xu/Control-esp32/Structure/物流小车底盘_v6/标准件/同步轮.SLDPRT

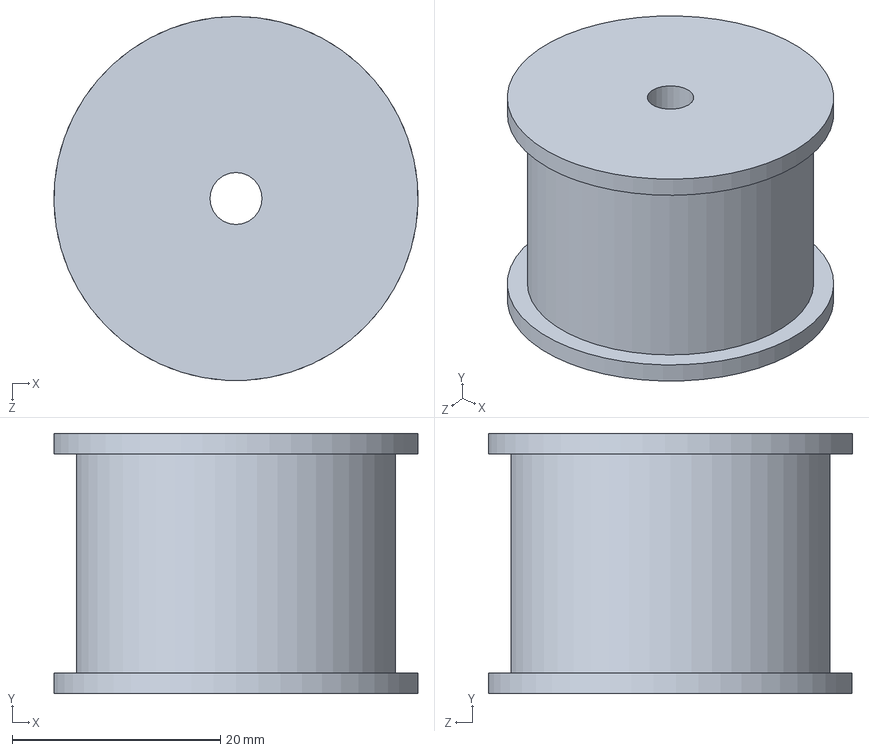
[picture p74: CAD file, 2026-09-05]
Structure/物流小车底盘_v6/标准件/同步轮.SLDPRT
35.0 x 25.0 x 35.0 mm
