jace-xu/Control-esp32/Structure/物流小车底盘_v6/配重铁块1.SLDPRT

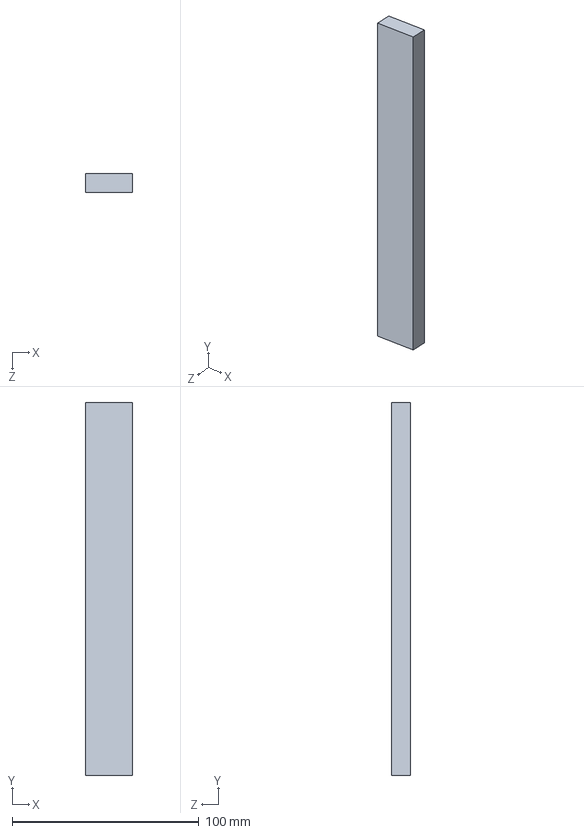
[picture p75: CAD file, 2026-09-05]
Structure/物流小车底盘_v6/配重铁块1.SLDPRT
25.0 x 200.0 x 10.0 mm
