jace-xu/Control-esp32/Structure/机械臂_v6/购买标准件/六面螺母_10.SLDPRT

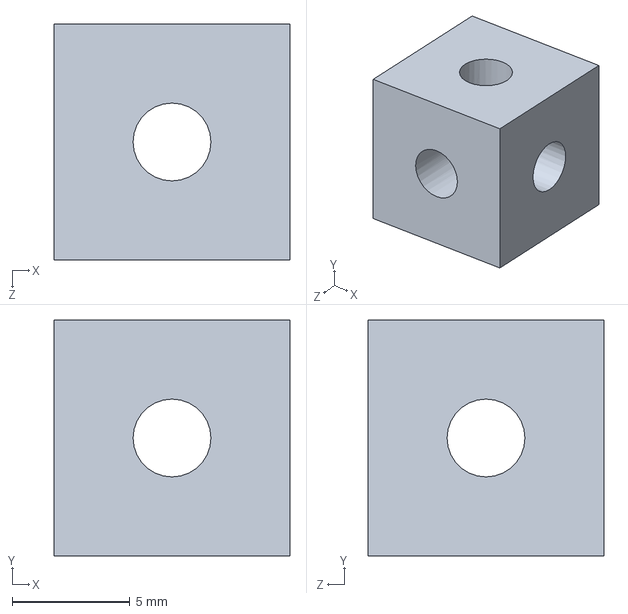
[picture p76: CAD file, 2026-09-05]
Structure/机械臂_v6/购买标准件/六面螺母_10.SLDPRT
10.0 x 10.0 x 10.0 mm
