jace-xu/Control-esp32/Structure/物流小车底盘_v6/esp32.SLDPRT

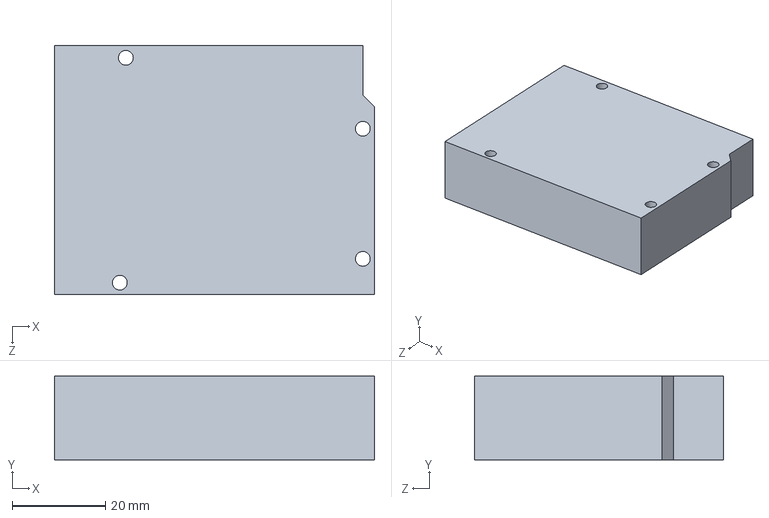
[picture p77: CAD file, 2026-09-05]
Structure/物流小车底盘_v6/esp32.SLDPRT
68.6 x 18.0 x 53.3 mm
