jace-xu/Control-esp32/Structure/物流小车底盘_v6/标准件/齿条50×1.SLDPRT

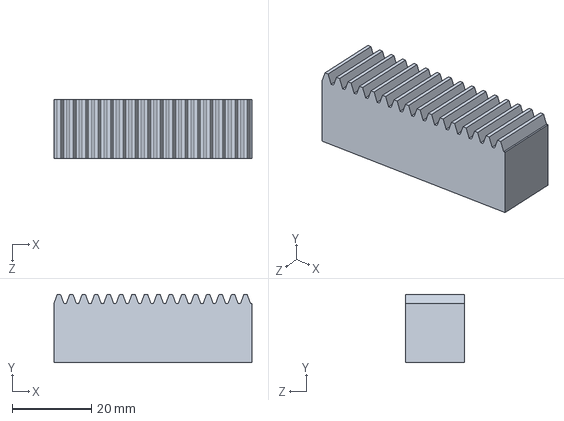
[picture p78: CAD file, 2026-09-05]
Structure/物流小车底盘_v6/标准件/齿条50×1.SLDPRT
50.0 x 17.2 x 15.0 mm
