jace-xu/Control-esp32/Structure/机械臂_v6/购买标准件/丝母座.SLDPRT

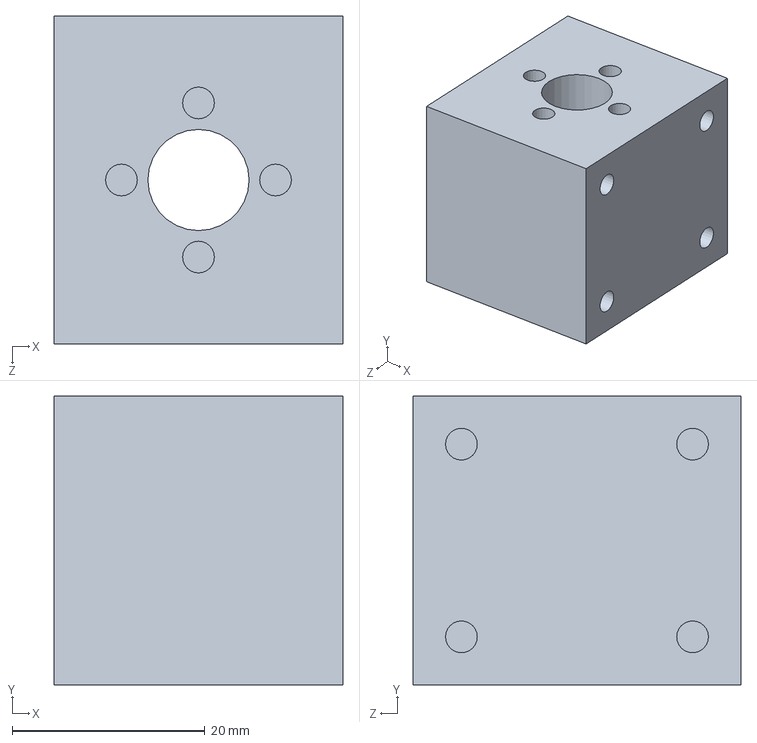
[picture p79: CAD file, 2026-09-05]
Structure/机械臂_v6/购买标准件/丝母座.SLDPRT
30.0 x 30.0 x 34.0 mm
