jace-xu/Control-esp32/Structure/物流小车底盘_v6/标准件/六角防松锁紧螺母.SLDPRT

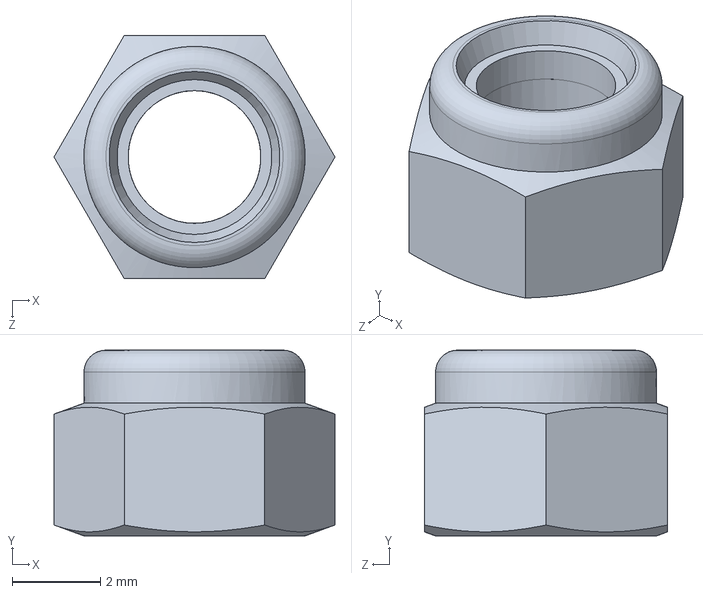
[picture p80: CAD file, 2026-09-05]
Structure/物流小车底盘_v6/标准件/六角防松锁紧螺母.SLDPRT
6.35 x 4.20 x 5.50 mm
