jace-xu/Control-esp32/Structure/机械臂_v6/购买标准件/线轨MGN9_标件_220.SLDPRT

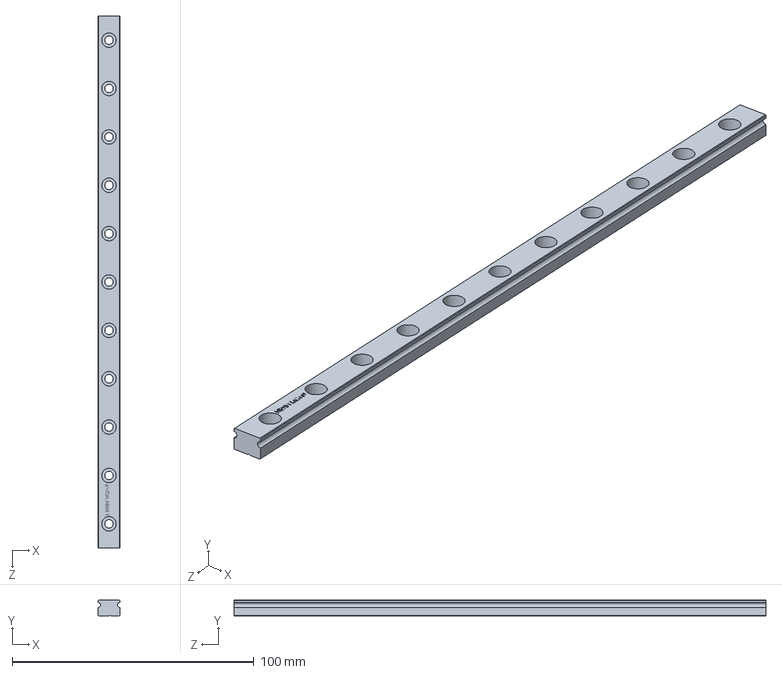
[picture p81: CAD file, 2026-09-05]
Structure/机械臂_v6/购买标准件/线轨MGN9_标件_220.SLDPRT
9.00 x 6.50 x 220.0 mm
