jace-xu/Control-esp32/Structure/物流小车底盘_v6/小车第一层.SLDPRT

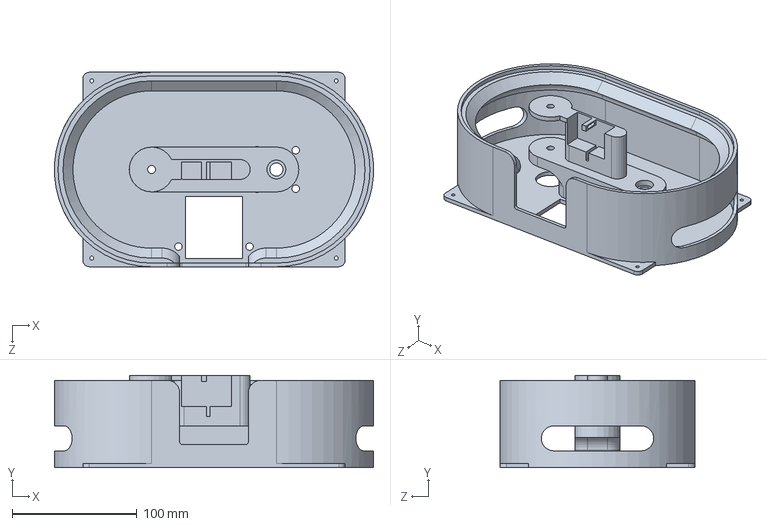
[picture p82: CAD file, 2026-09-05]
Structure/物流小车底盘_v6/小车第一层.SLDPRT
255.7 x 74.0 x 156.0 mm
