jace-xu/Control-esp32/Structure/机械臂_v6/购买标准件/2020型材角码.SLDPRT

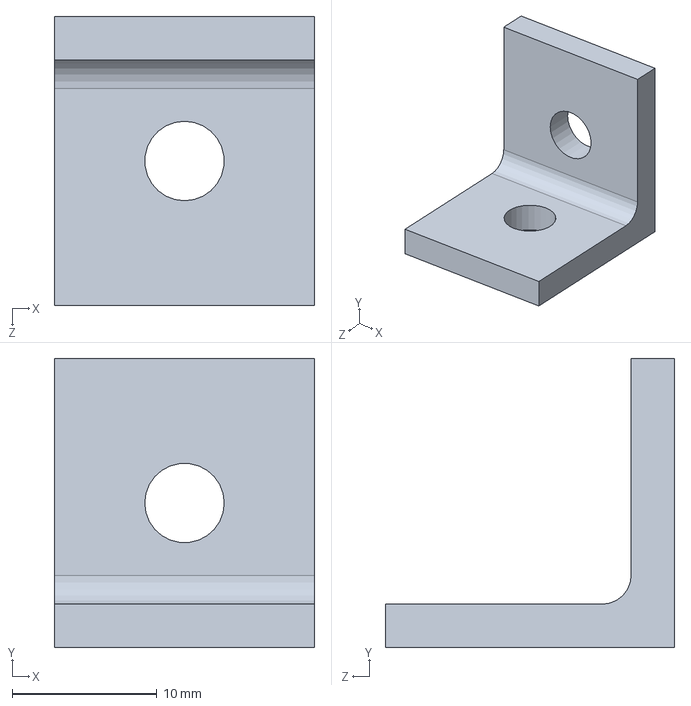
[picture p83: CAD file, 2026-09-05]
Structure/机械臂_v6/购买标准件/2020型材角码.SLDPRT
18.0 x 20.0 x 20.0 mm
