jace-xu/Control-esp32/Structure/物流小车底盘_v6/rpi4b.SLDPRT

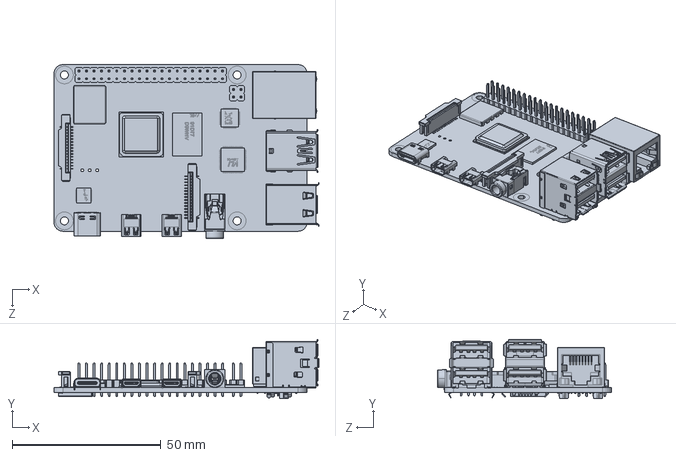
[picture p84: CAD file, 2026-09-05]
Structure/物流小车底盘_v6/rpi4b.SLDPRT
89.0 x 19.9 x 58.4 mm
