jace-xu/Control-esp32/Structure/机械臂_v6/购买标准件/滑块MGN9C_标件_01.SLDPRT

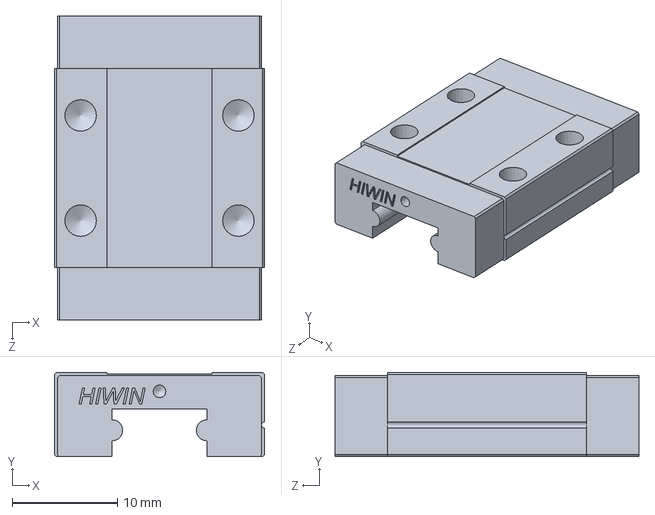
[picture p85: CAD file, 2026-09-05]
Structure/机械臂_v6/购买标准件/滑块MGN9C_标件_01.SLDPRT
20.0 x 8.00 x 28.9 mm
