jace-xu/Control-esp32/Structure/物流小车底盘_v6/纵向支撑板.SLDPRT

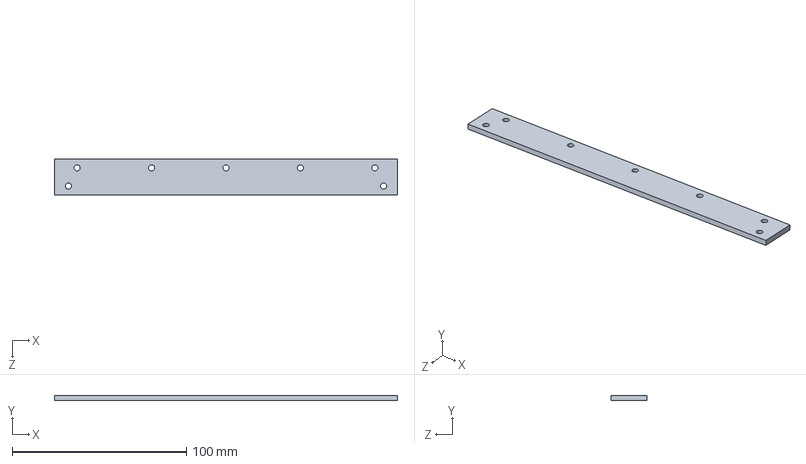
[picture p87: CAD file, 2026-09-05]
Structure/物流小车底盘_v6/纵向支撑板.SLDPRT
197.0 x 3.00 x 20.5 mm
