jace-xu/Control-esp32/Structure/机械臂_v6/购买标准件/光轴_5_42.SLDPRT

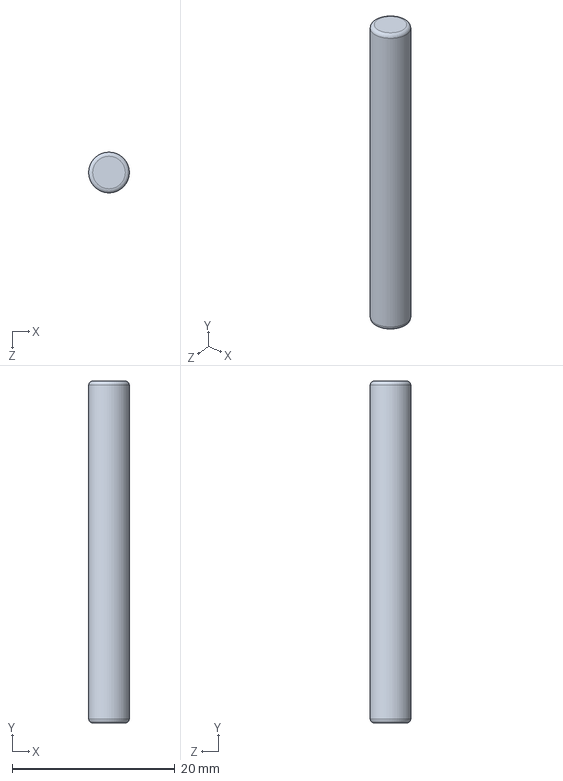
[picture p88: CAD file, 2026-09-05]
Structure/机械臂_v6/购买标准件/光轴_5_42.SLDPRT
4.99 x 42.0 x 5.00 mm
