jace-xu/Control-esp32/Structure/物流小车底盘_v6/齿条连接件.SLDPRT

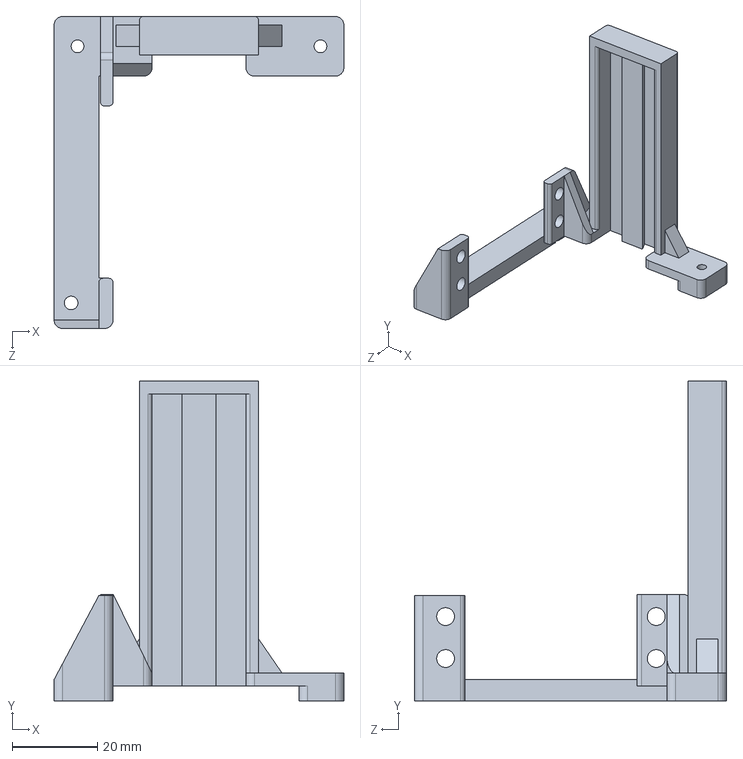
[picture p89: CAD file, 2026-09-05]
Structure/物流小车底盘_v6/齿条连接件.SLDPRT
68.0 x 75.0 x 73.2 mm
