jace-xu/Control-esp32/Structure/机械臂_v6/购买标准件/mg90舵机.SLDPRT

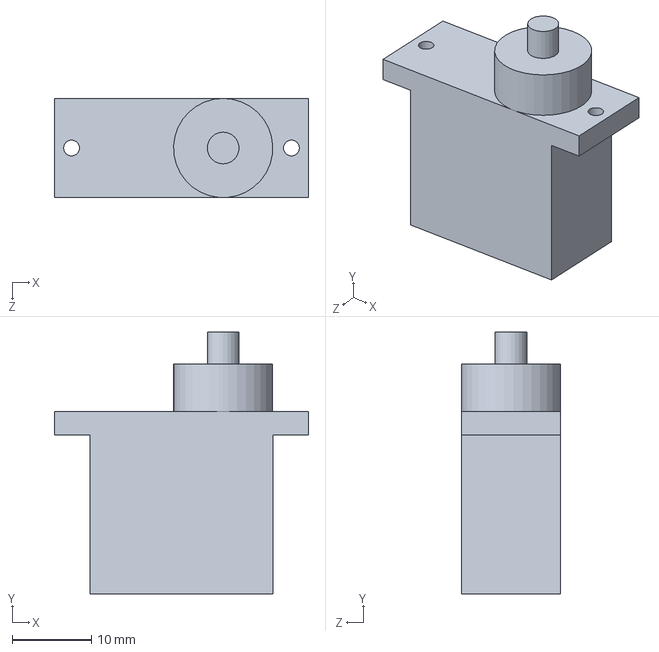
[picture p90: CAD file, 2026-09-05]
Structure/机械臂_v6/购买标准件/mg90舵机.SLDPRT
32.0 x 33.0 x 12.5 mm
