jace-xu/Control-esp32/Structure/物流小车底盘_v6/电机垫片.SLDPRT

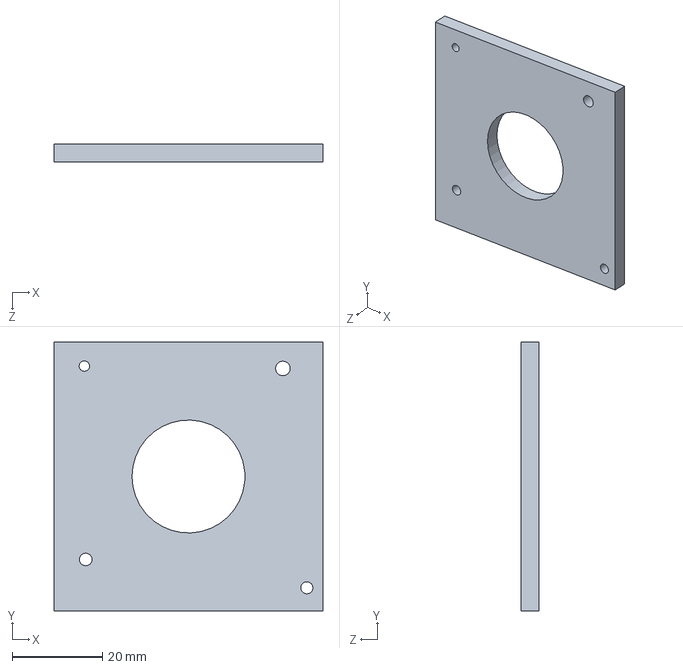
[picture p91: CAD file, 2026-09-05]
Structure/物流小车底盘_v6/电机垫片.SLDPRT
59.6 x 59.6 x 4.00 mm
