jace-xu/Control-esp32/Structure/机械臂_v6/购买标准件/轴套_5mm.SLDPRT

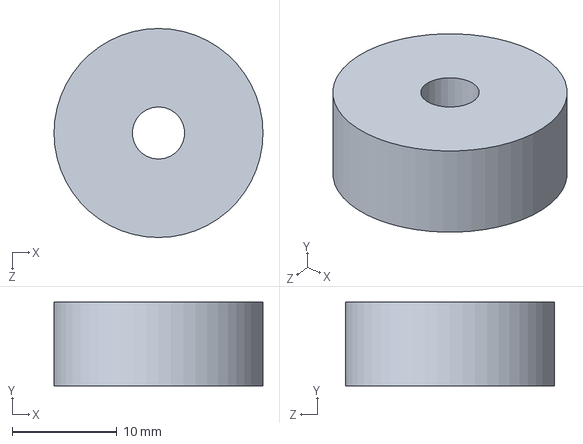
[picture p92: CAD file, 2026-09-05]
Structure/机械臂_v6/购买标准件/轴套_5mm.SLDPRT
20.0 x 8.00 x 20.0 mm
