jace-xu/Control-esp32/Structure/机械臂_v6/购买标准件/轴承座.SLDPRT

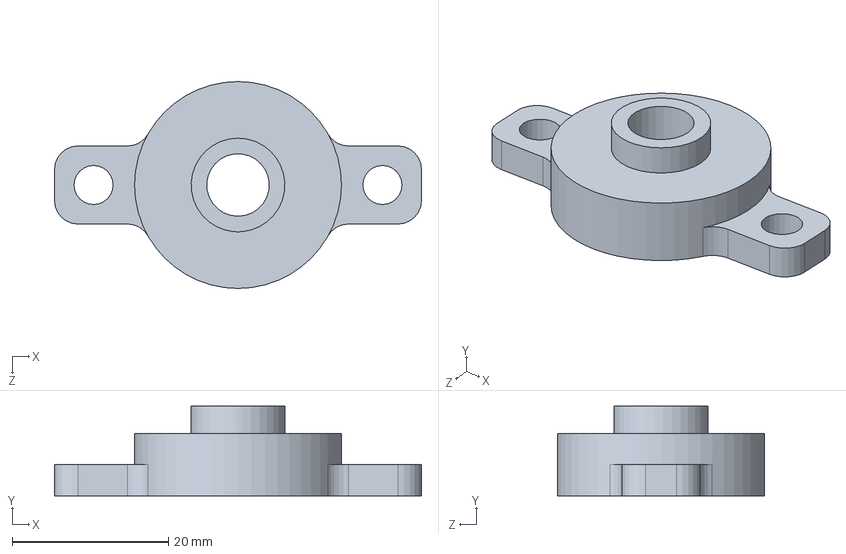
[picture p93: CAD file, 2026-09-05]
Structure/机械臂_v6/购买标准件/轴承座.SLDPRT
47.0 x 11.5 x 26.5 mm
