jace-xu/Control-esp32/Structure/机械臂_v6/购买标准件/回转轴承.SLDPRT

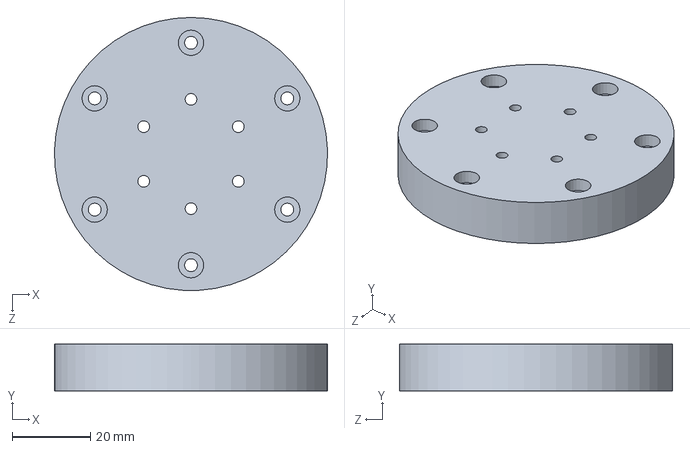
[picture p94: CAD file, 2026-09-05]
Structure/机械臂_v6/购买标准件/回转轴承.SLDPRT
70.0 x 12.0 x 70.0 mm
