jace-xu/Control-esp32/Structure/机械臂_v6/购买标准件/法兰联轴器_5mm.SLDPRT

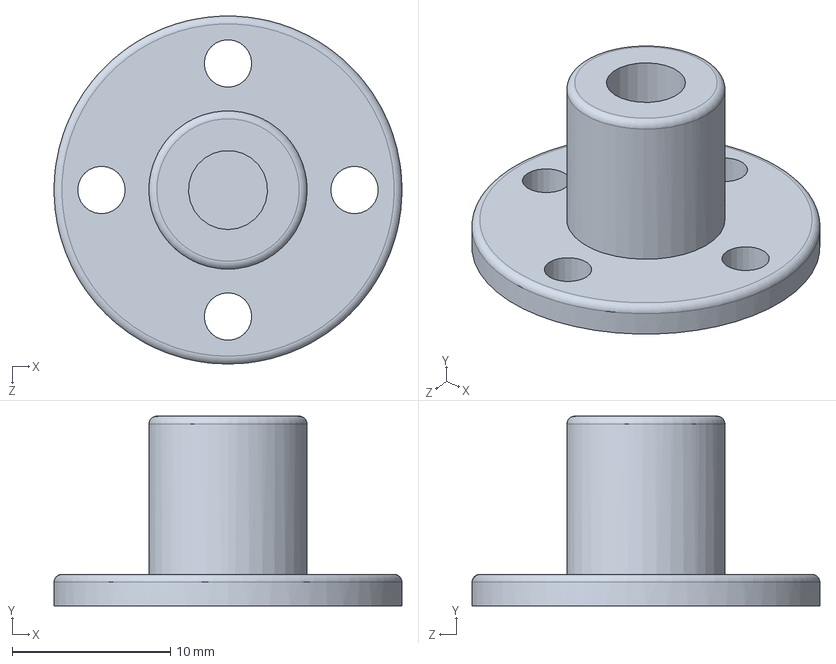
[picture p95: CAD file, 2026-09-05]
Structure/机械臂_v6/购买标准件/法兰联轴器_5mm.SLDPRT
22.0 x 12.0 x 22.0 mm
