jace-xu/Control-esp32/Structure/机械臂_v6/.吊臂装配体.SLDASM

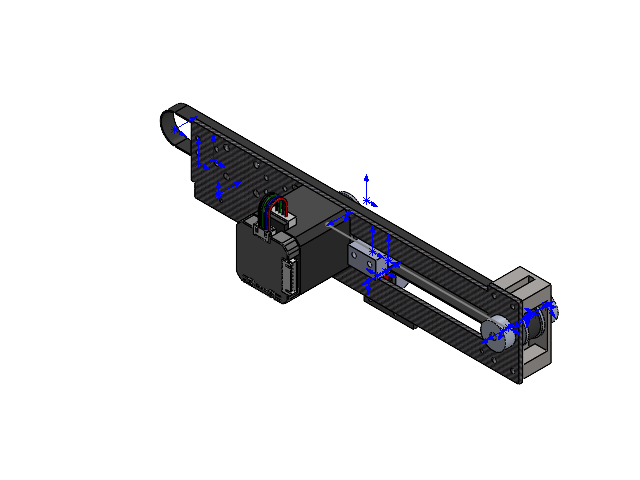
[picture p99: CAD file, 2026-09-05]
Structure/机械臂_v6/.吊臂装配体.SLDASM
夹爪背板_3mm
ZDT_X42_L40Motor
同步带轮_24H3M x 2
滑块MGN7C_标件_01
法兰轴承_10_5 x 2
光轴_5_42
轴套_5mm x 2
同步带_10mm
六面螺母_10 x 2
夹爪固定板_3mm
夹爪同步带连接
线轨MGN7_标件_235
吊臂从动轮外侧固定_打印版
