jace-xu/Control-esp32/Structure/机械臂_v6/机械臂装配体.SLDASM

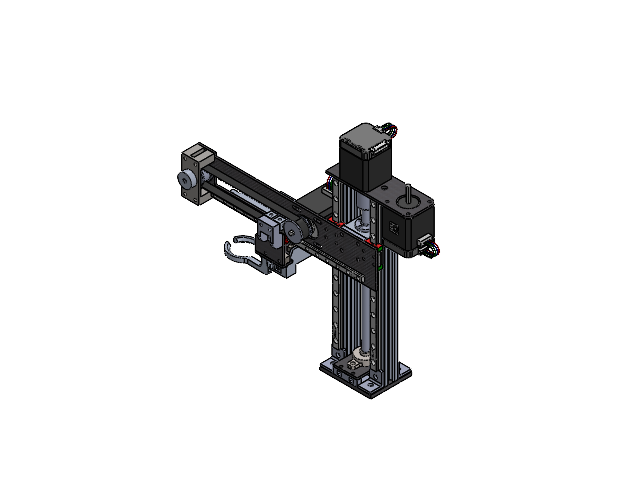
[picture p100: CAD file, 2026-09-05]
Structure/机械臂_v6/机械臂装配体.SLDASM
旋转台底板_5mm
2020型材角码 x 4
线轨MGN9_标件_220 x 2
滑块MGN9C_标件_01 x 2
ZDT_X42_L40Motor x 3
型材顶部板_3mm
丝杆_8_250
丝杆螺母
丝母座
z轴机械臂垫块
欧标2020_240_后
欧标2020_240_前
法兰联轴器_5mm
下部轴承底板
丝杆轴承安装板_3mm
轴承座
轴承垫块
夹爪背板_3mm
同步带轮_24H3M x 2
滑块MGN7C_标件_01
法兰轴承_10_5 x 2
光轴_5_42
轴套_5mm x 2
同步带_10mm
六面螺母_10 x 2
夹爪固定板_3mm
夹爪同步带连接
线轨MGN7_标件_235
吊臂从动轮外侧固定_打印版
六面螺母_板材连接_6mm x 2
夹爪左
夹爪右
舵机支架
mg90舵盘
mg90舵机
夹爪连接板_3mm
轴承_5 x 2
六面螺母_板材连接_8mm
联轴器_顶部
