jace-xu/Control-esp32/Structure/机械臂_v6/.夹爪装配体.SLDASM

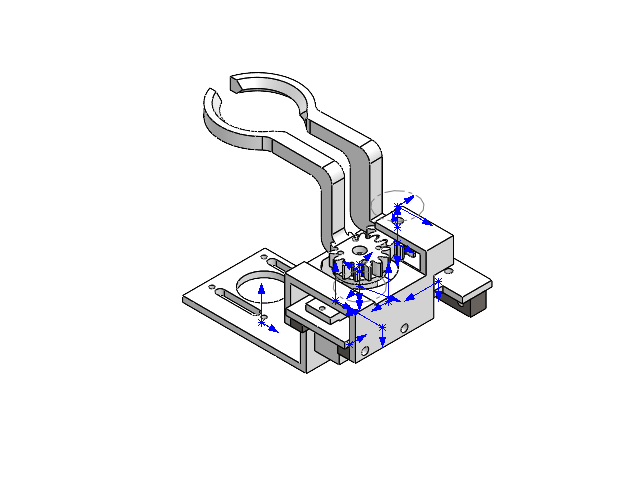
[picture p101: CAD file, 2026-09-05]
Structure/机械臂_v6/.夹爪装配体.SLDASM
六面螺母_板材连接_6mm x 2
夹爪左
夹爪右
舵机支架
mg90舵盘
mg90舵机
夹爪连接板_3mm
轴承_5 x 2
六面螺母_板材连接_8mm
