jace-xu/Control-esp32/Structure/物流小车底盘_v6/物料盘装配体.SLDASM

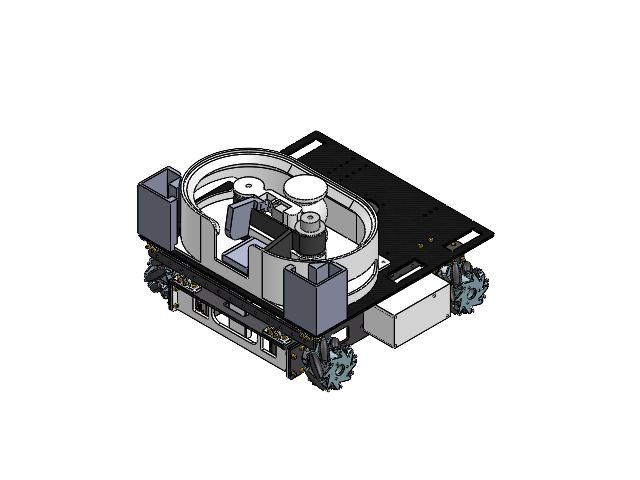
[picture p102: CAD file, 2026-09-05]
Structure/物流小车底盘_v6/物料盘装配体.SLDASM
同步轮
同步轮惰轮
联轴器
同步带
舵机
小车第一层
板材
齿条连接件
齿条连接件_顶板
齿条50×1
圆柱齿轮18×1
60mm麦轮_右 x 2
60mm麦轮_左 x 2
麦轮联轴器 x 4
电机连接板_前 x 2
42步进电机 x 4
内六角圆柱头螺钉 x 74
六角防松锁紧螺母 x 48
电机连接板_后 x 2
牛眼轮 x 2
电机板固定件_牛眼轮架
电机板固定件 x 3
悬挂_半 x 2
M4x8_内六角机牙螺丝 x 8
层连接件 x 4
层连接板_1
M3_16+32_H8_L48 x 2
底板_前
底板_后
铜柱_m2.5_10 x 3
rpi4b
电池仓
纵向支撑板
降压板
esp32
ZDT扩展
ZDT_X42_L40Motor
电机垫片
物料
mg90舵机
物料挡板
铁块托盘
Mirror铁块托盘
